kholia/HF-PA-v6/Info/5-watt-qrp-gallon-amplifier-hf-using-irf510.pdf

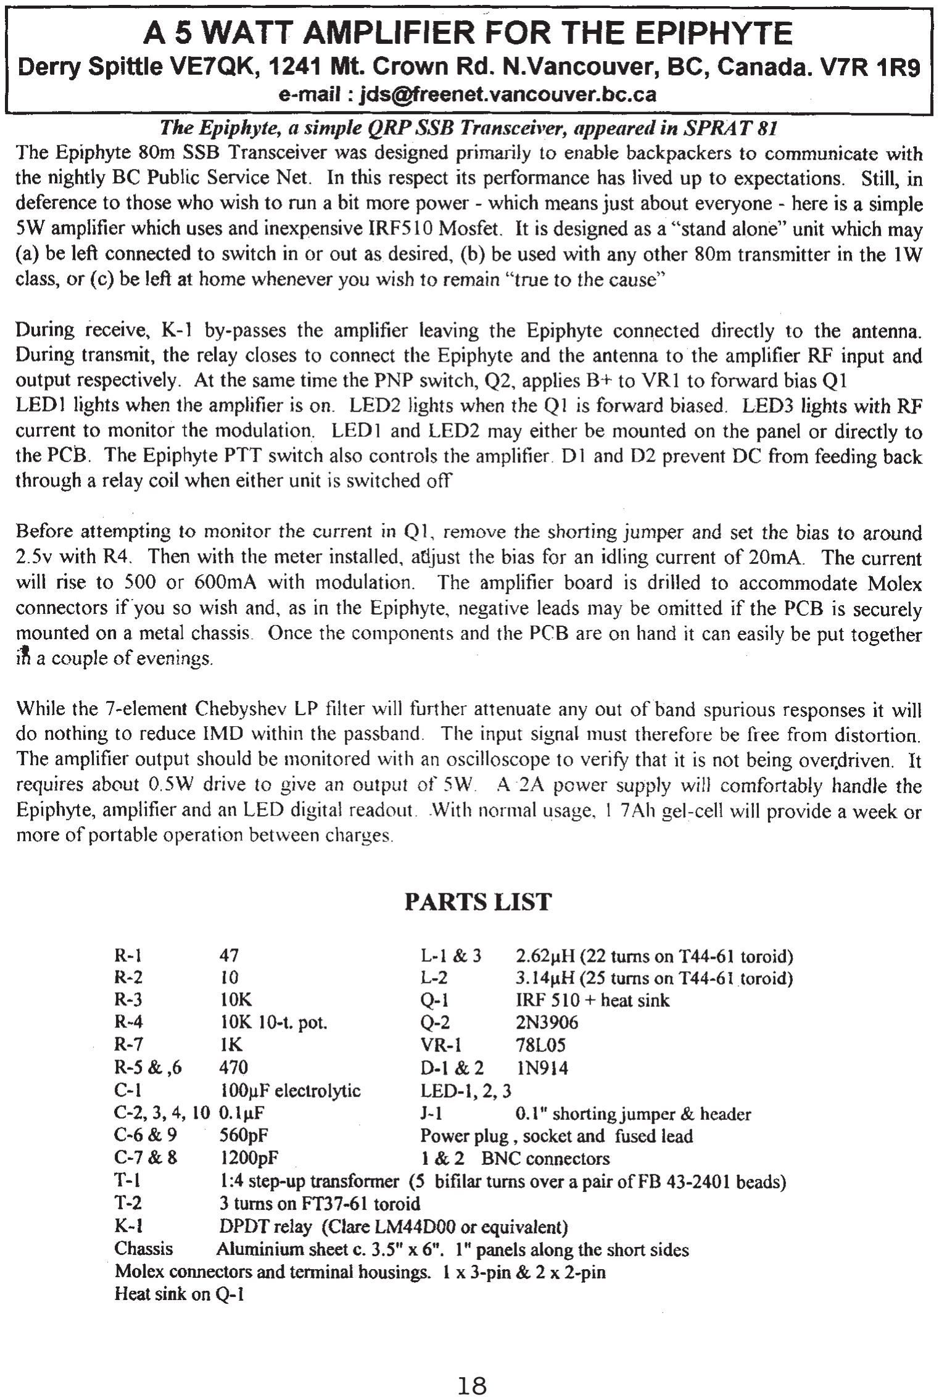
[picture p87: page 1]

18

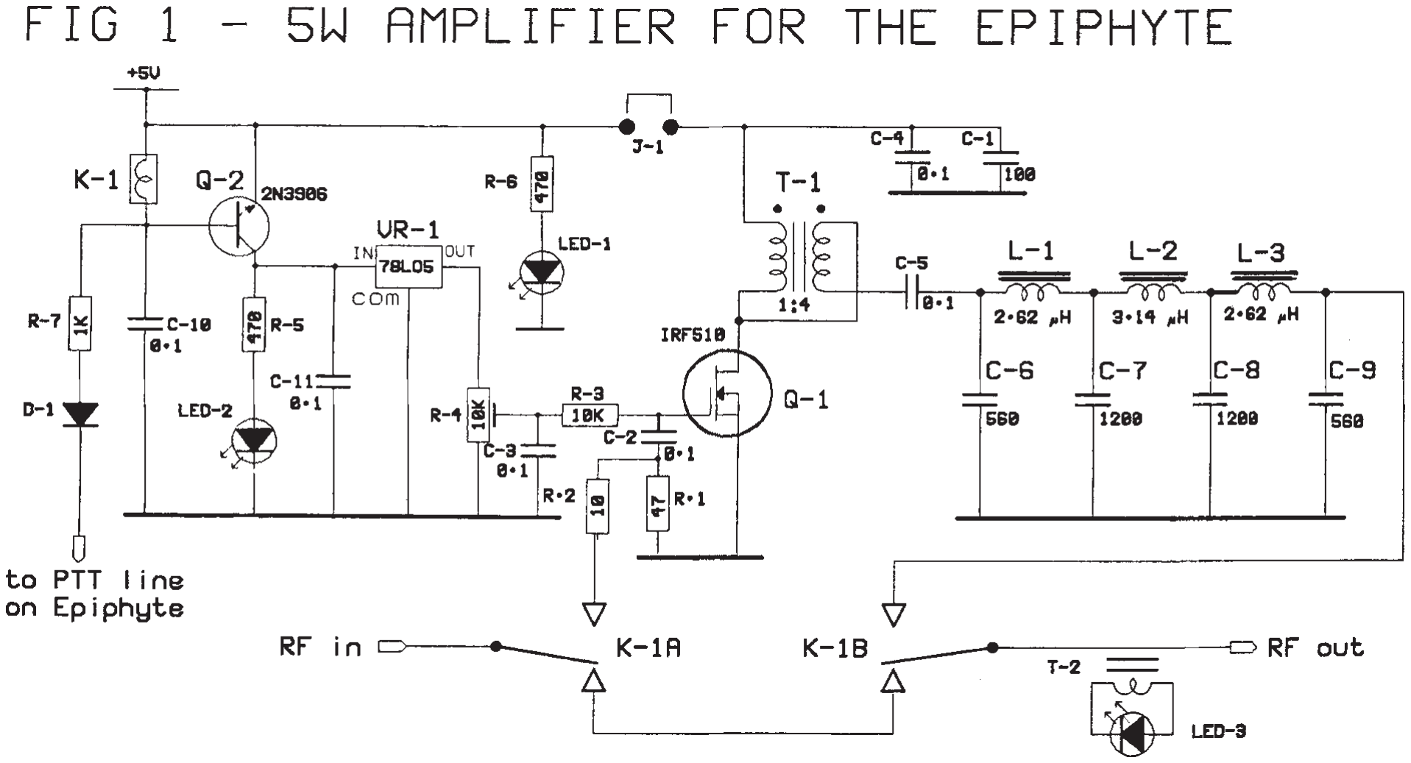
[picture p88: figure]

19

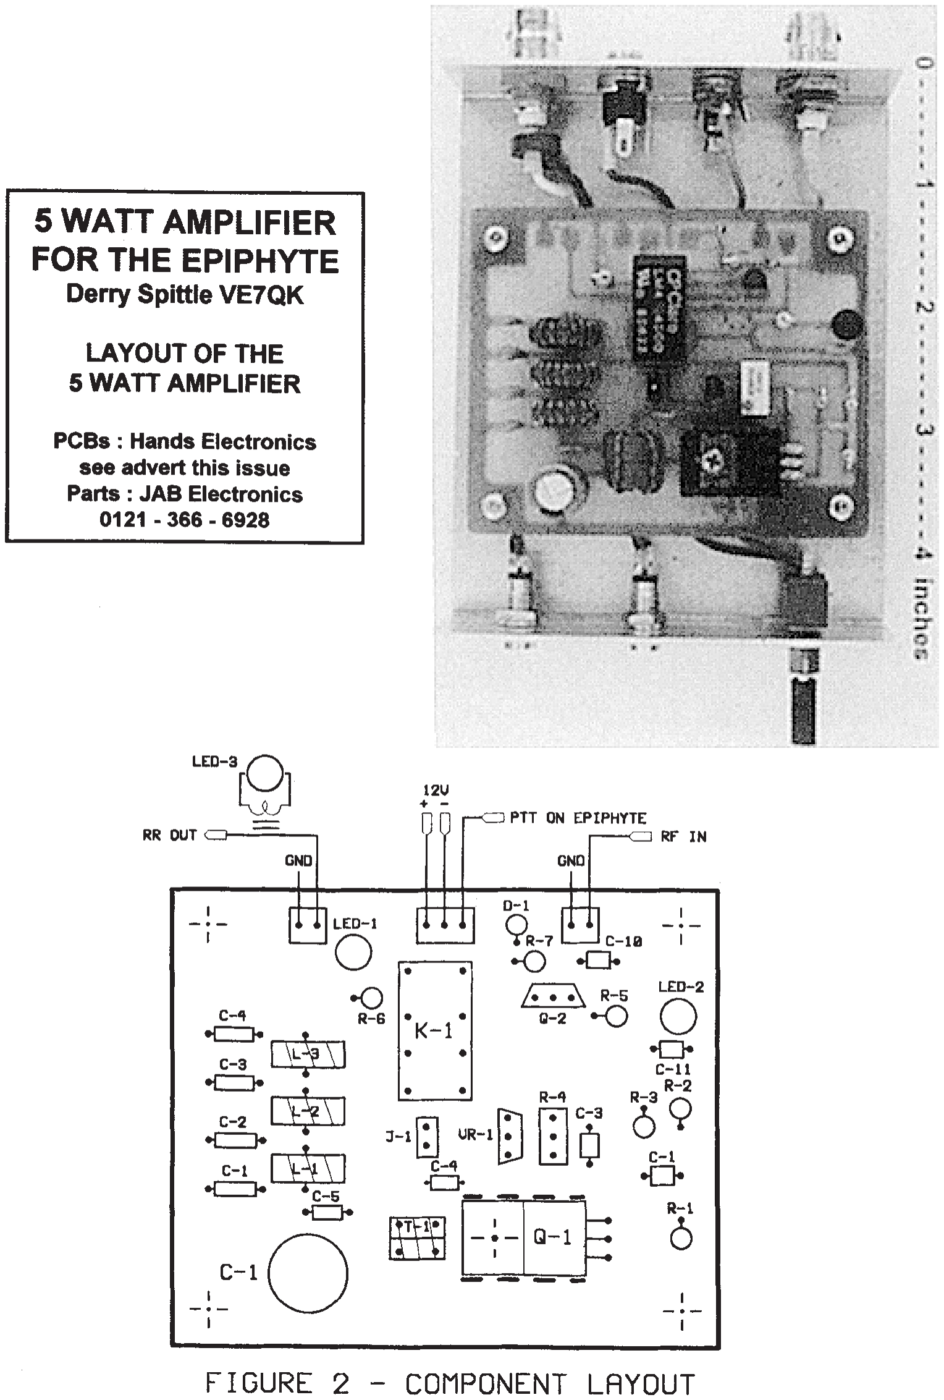
[picture p89: page 3]

20
