kholia/HF-PA-v6/datasheets/IRF9540-Pinout.jpg

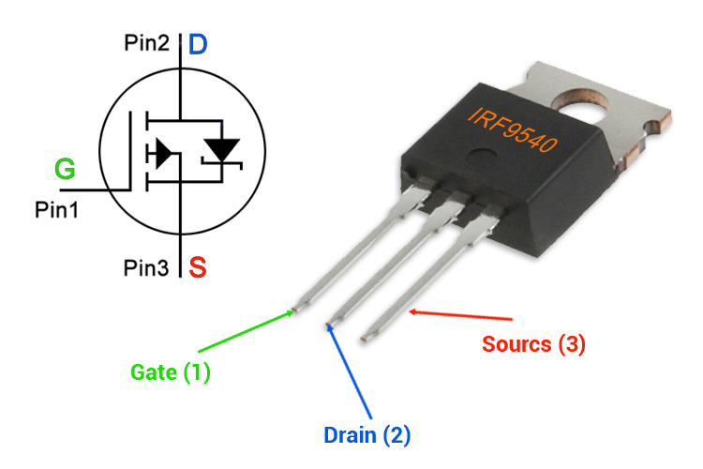
datasheets/IRF9540-Pinout.jpg
