kholia/HF-PA-v6/datasheets/Pinout of 2N2222 variants in plastic TO-92 package.jpg

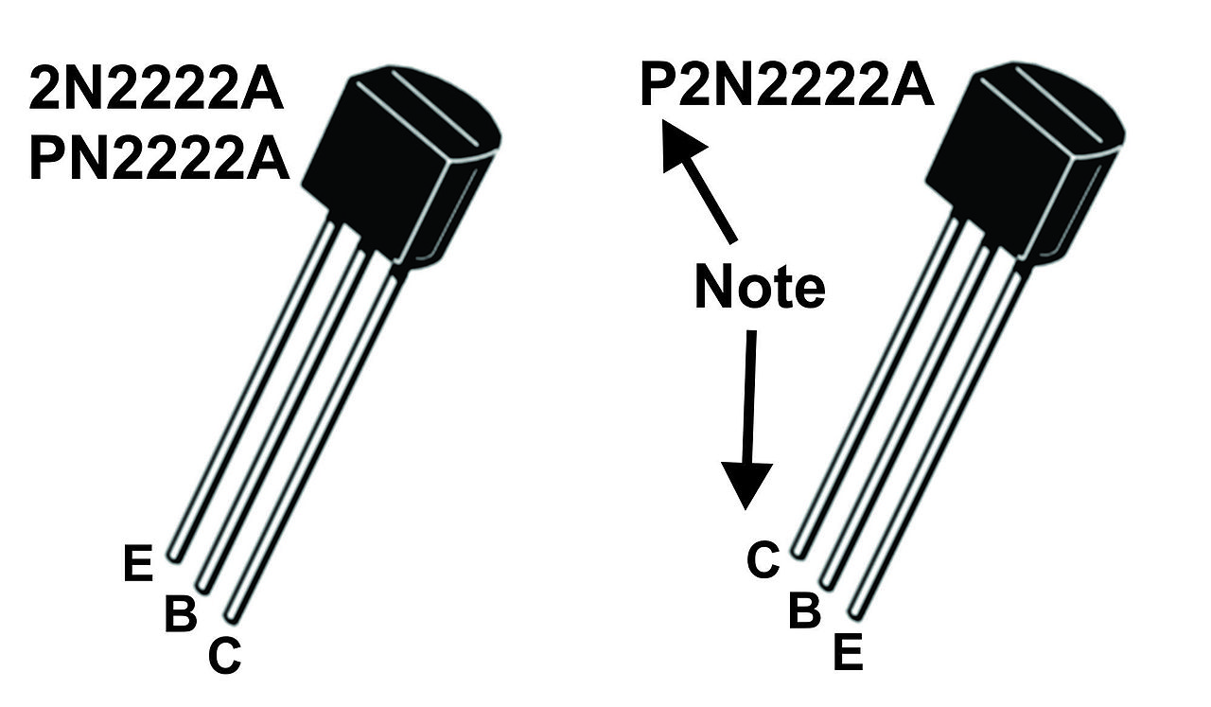
datasheets/Pinout of 2N2222 variants in plastic TO-92 package.jpg
