kholia/HF-PA-v6/datasheets/rd16hhf1-pout-vs-pin.png

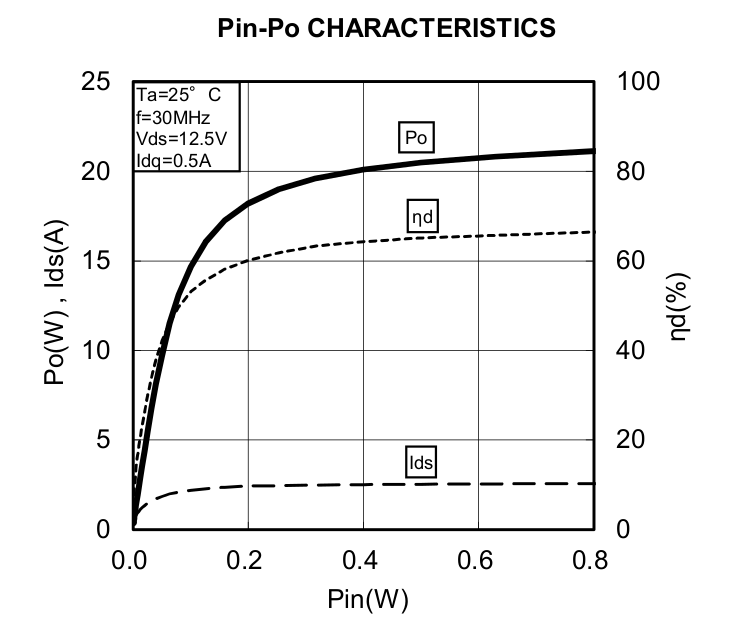
datasheets/rd16hhf1-pout-vs-pin.png
