kholia/HF-PA-v6/HF-PA-Combined/PCB-Rendering.png

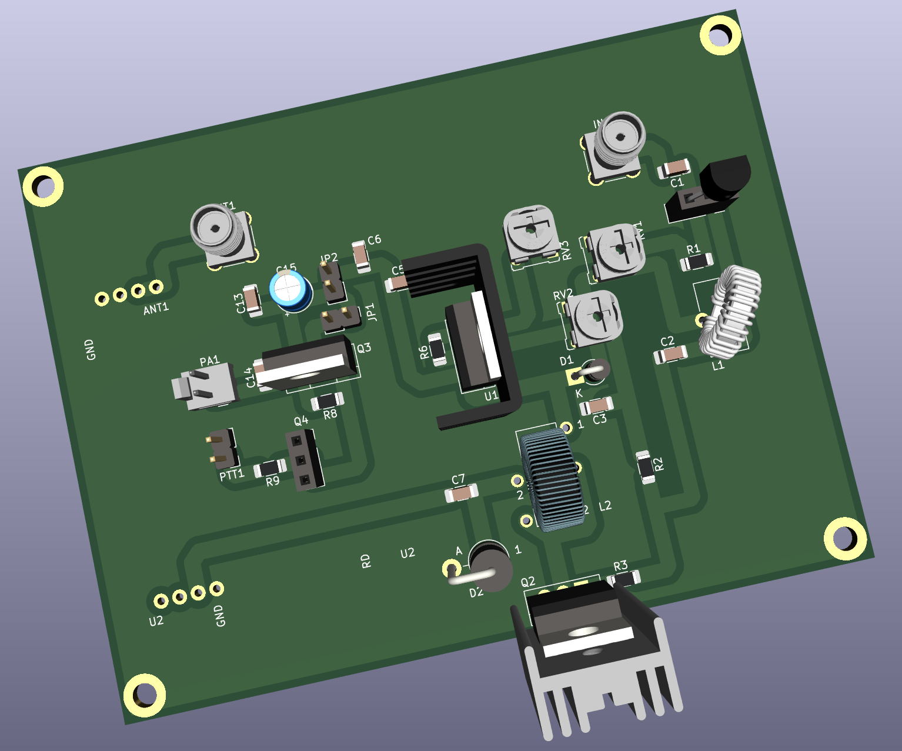
HF-PA-Combined/PCB-Rendering.png
