kholia/HF-PA-v6/Info/1W_PA_Hand_Schematic.jpg

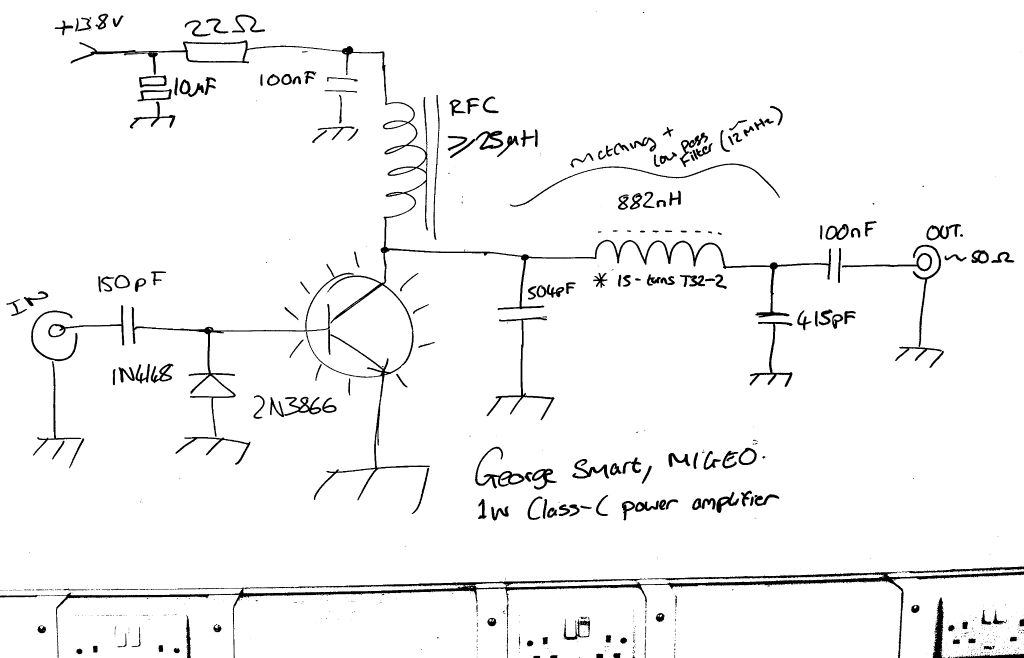
Info/1W_PA_Hand_Schematic.jpg
