kholia/HF-PA-v6/Info/1W_PA_Picture.jpg

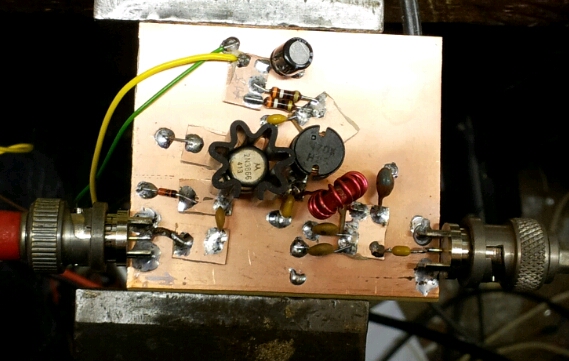
Info/1W_PA_Picture.jpg
