kholia/HF-PA-v6/Info/50MHZ_16W_MOSFET_PA.gif

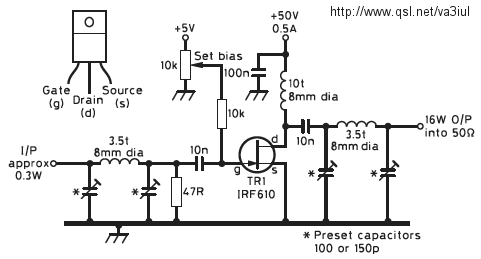
Info/50MHZ_16W_MOSFET_PA.gif
