kholia/HF-PA-v6/Info/50MHz_40W_MOSFET_PA_DJ9FG.gif

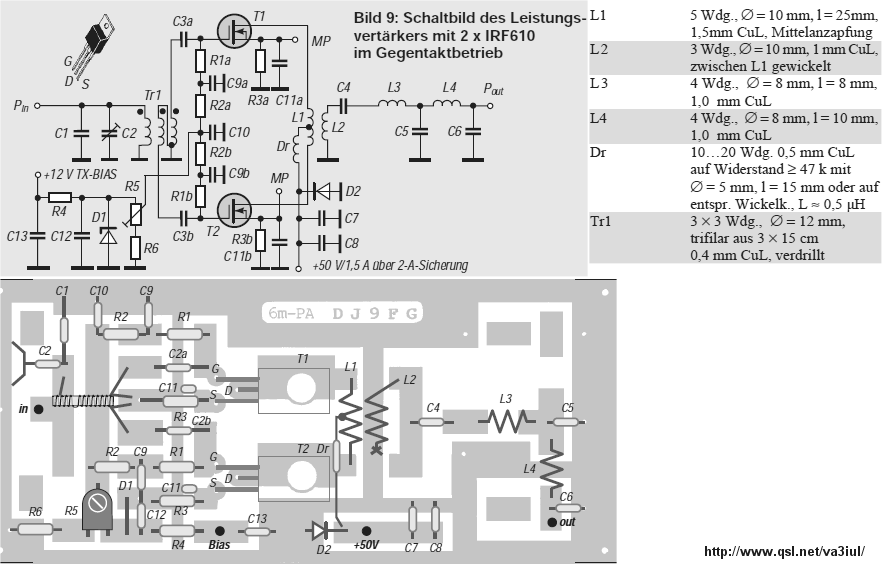
Info/50MHz_40W_MOSFET_PA_DJ9FG.gif
