kholia/HF-PA-v6/Info/"Idq".png

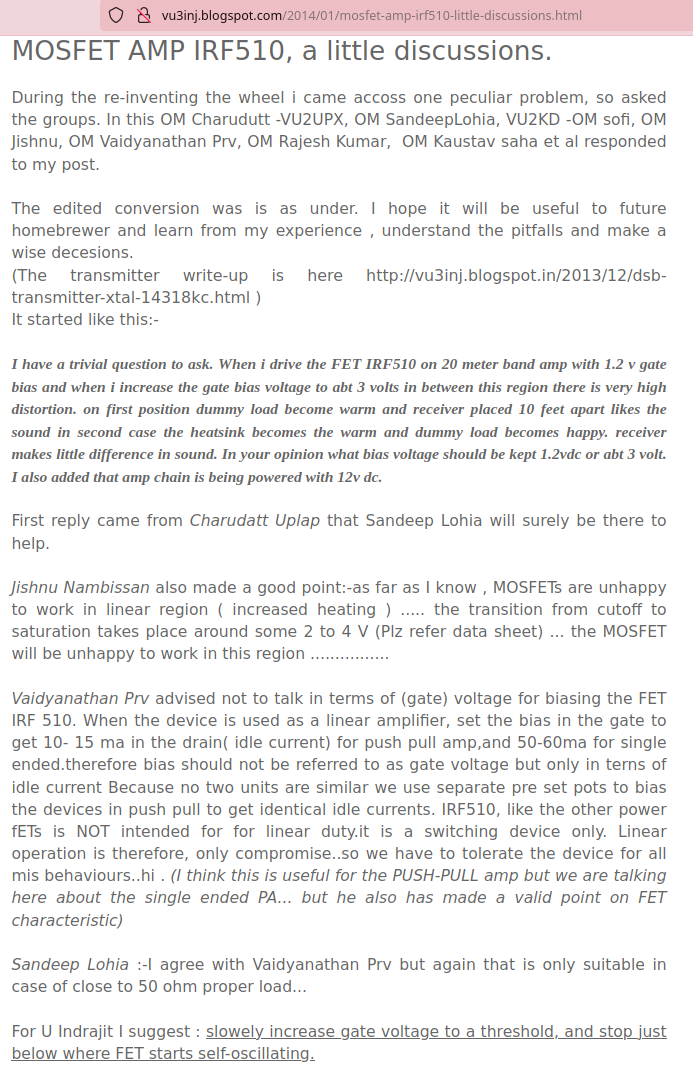
Info/"Idq".png
