kholia/HF-PA-v6/Info/(220)_ZX-SSB_II_PA.png

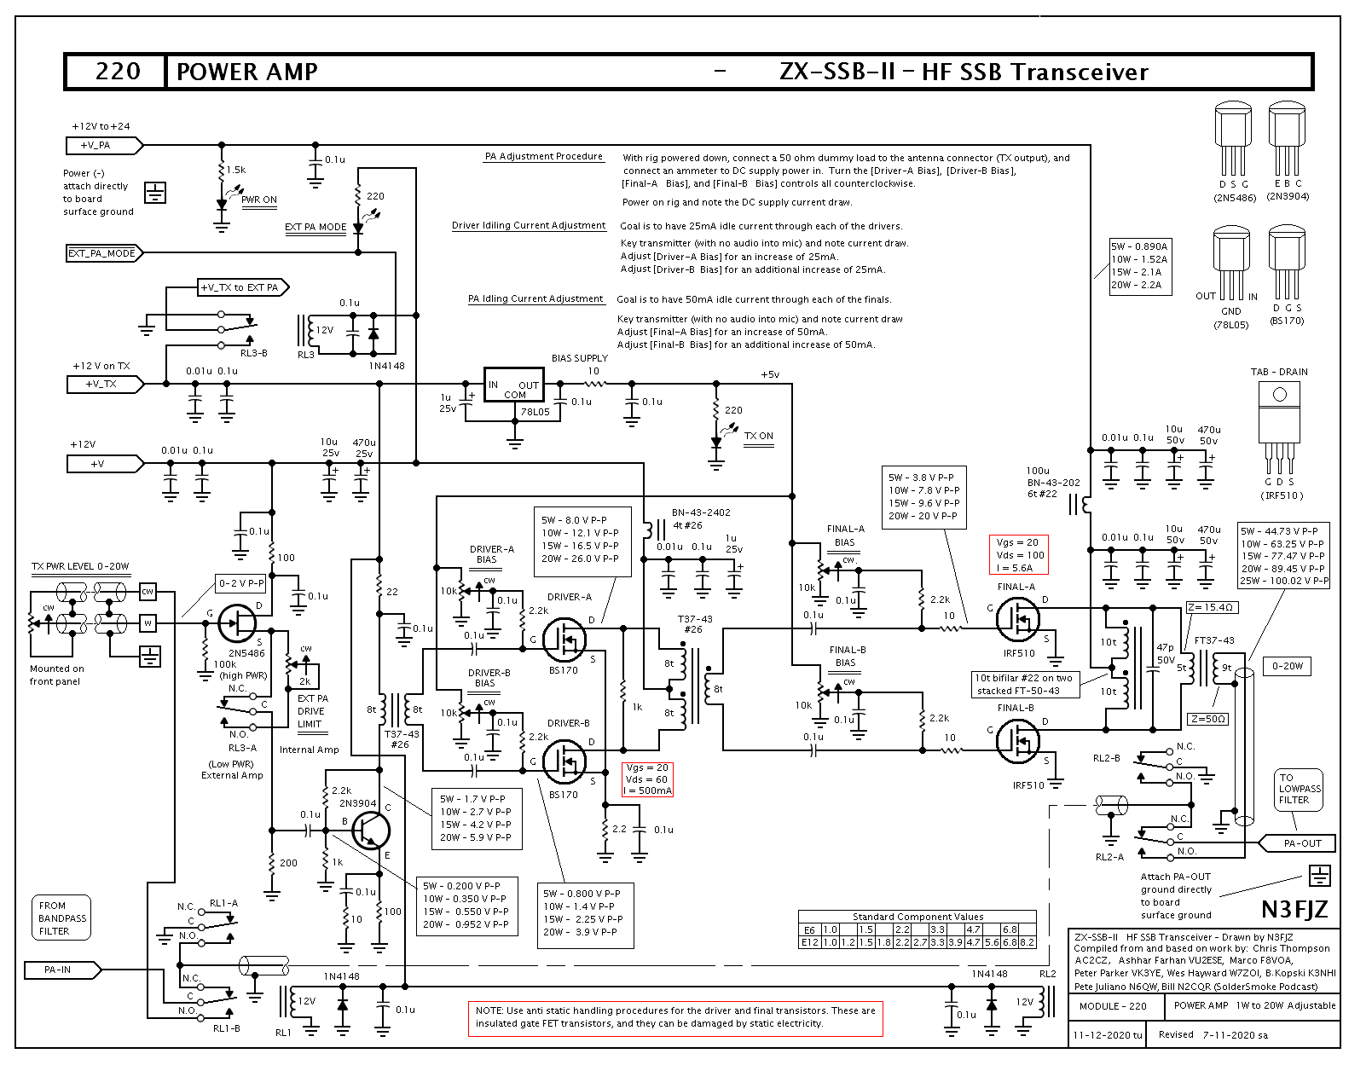
Info/(220)_ZX-SSB_II_PA.png
