kholia/HF-PA-v6/Info/(230-ALL)_ZX-SSB-II_Lowpass_filter_all_bands.png

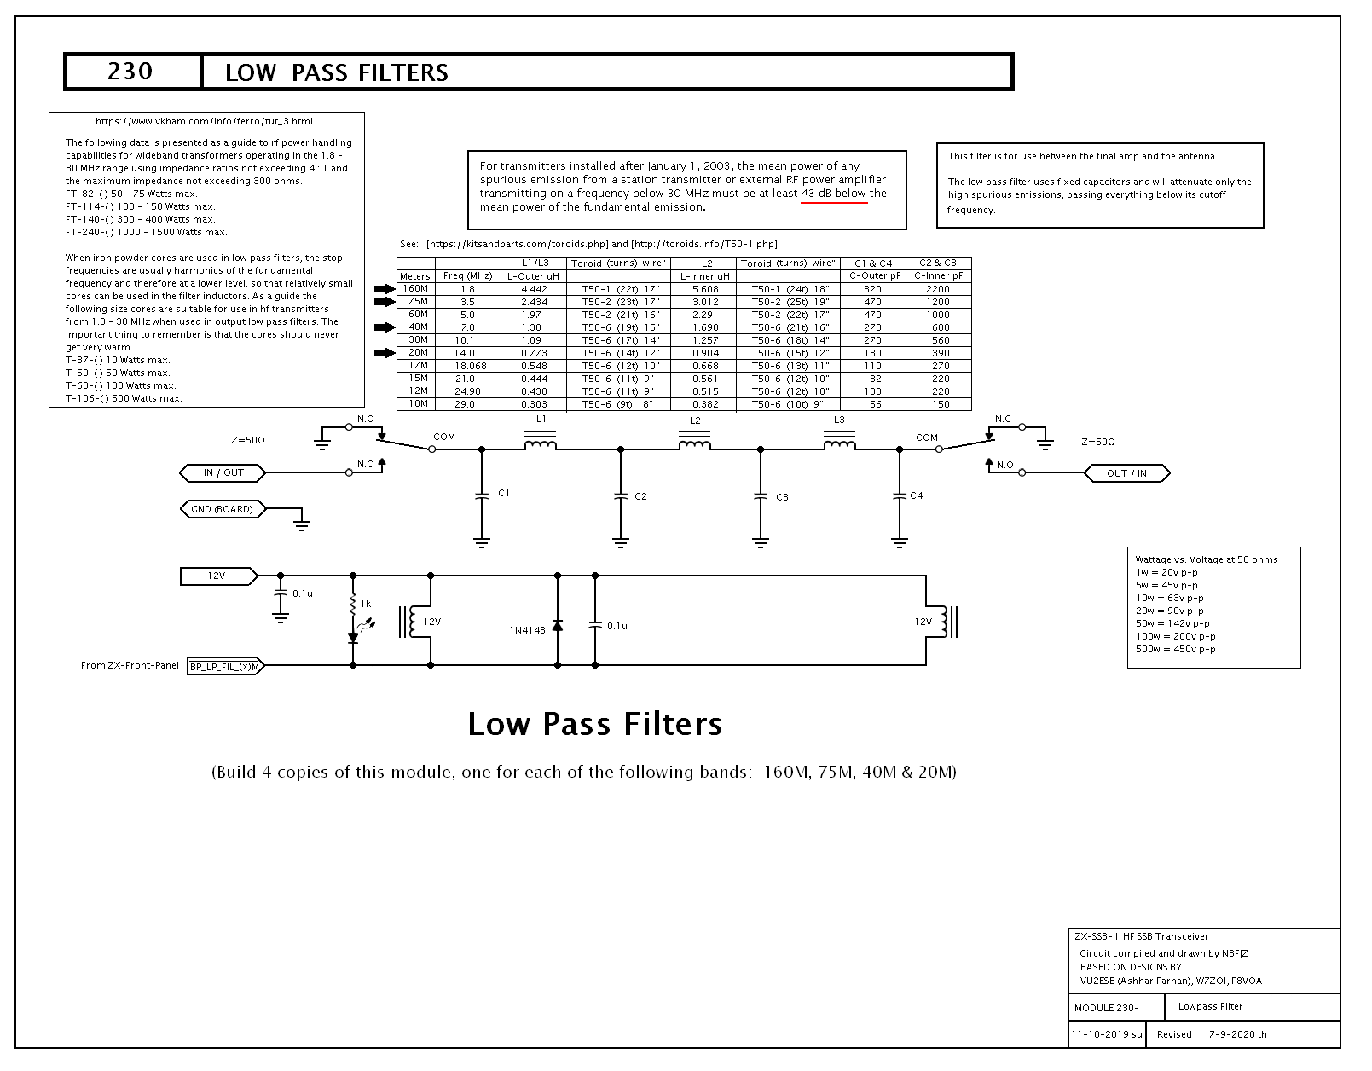
Info/(230-ALL)_ZX-SSB-II_Lowpass_filter_all_bands.png
