kholia/HF-PA-v6/Info/Ampacity-Screenshot_2021-09-23_20-11-56.png

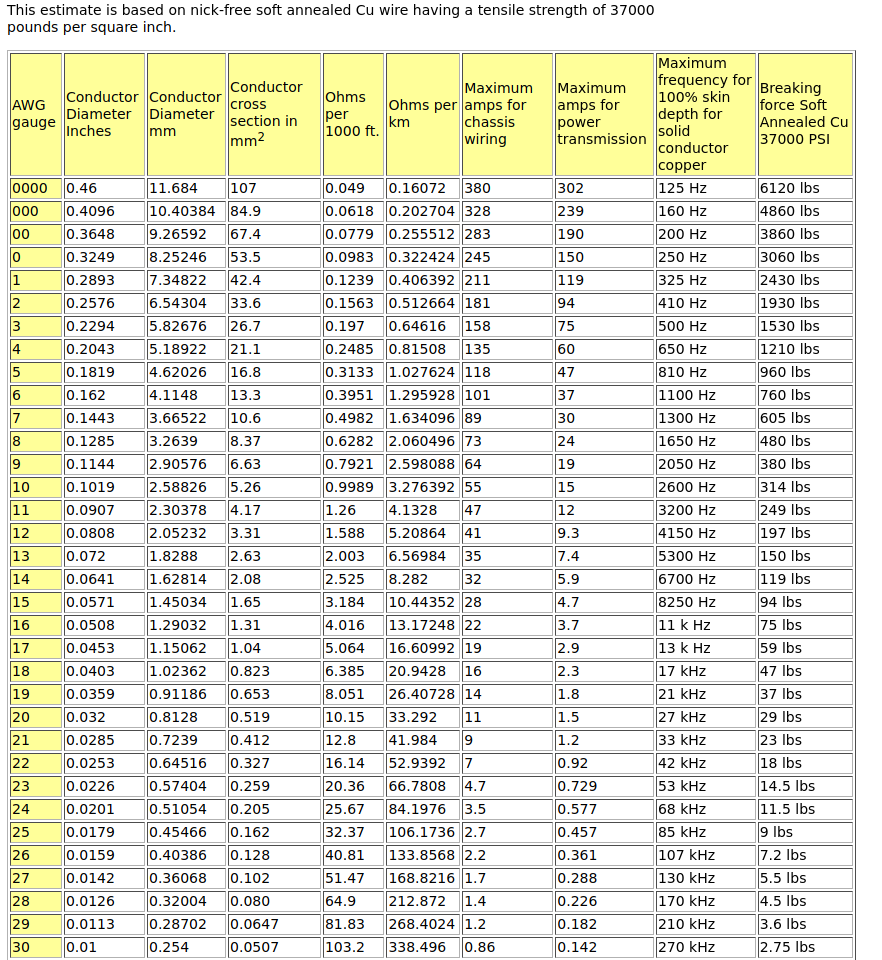
Info/Ampacity-Screenshot_2021-09-23_20-11-56.png
