kholia/HF-PA-v6/Info/BD139 Note.png

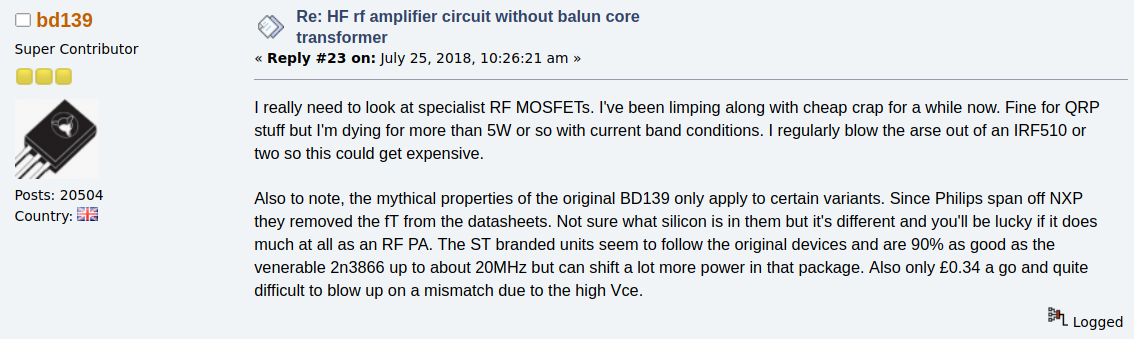
Info/BD139 Note.png
