kholia/HF-PA-v6/Info/Fake 7805 CV - Mar 2018.jpeg

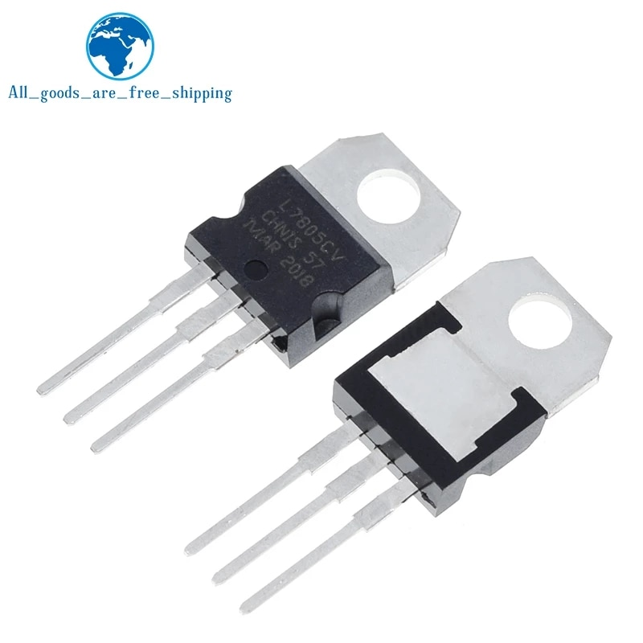
Info/Fake 7805 CV - Mar 2018.jpeg
