kholia/HF-PA-v6/Info/Fake ST 7805 - 1718.jpg

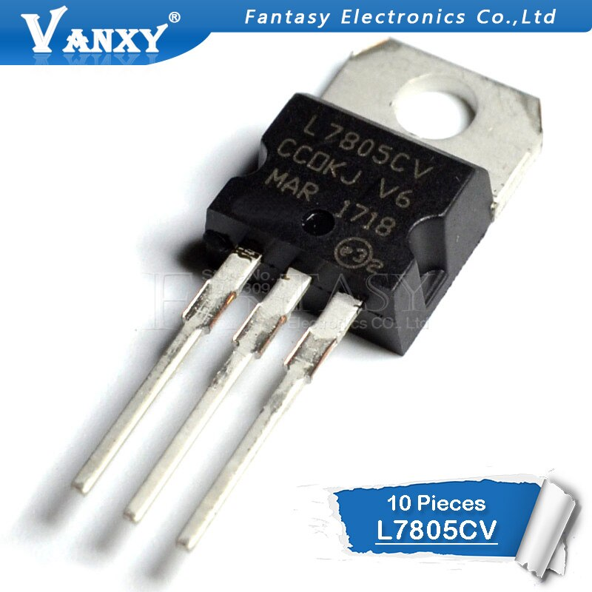
Info/Fake ST 7805 - 1718.jpg
