kholia/HF-PA-v6/Info/Fake ST 7805.jpg

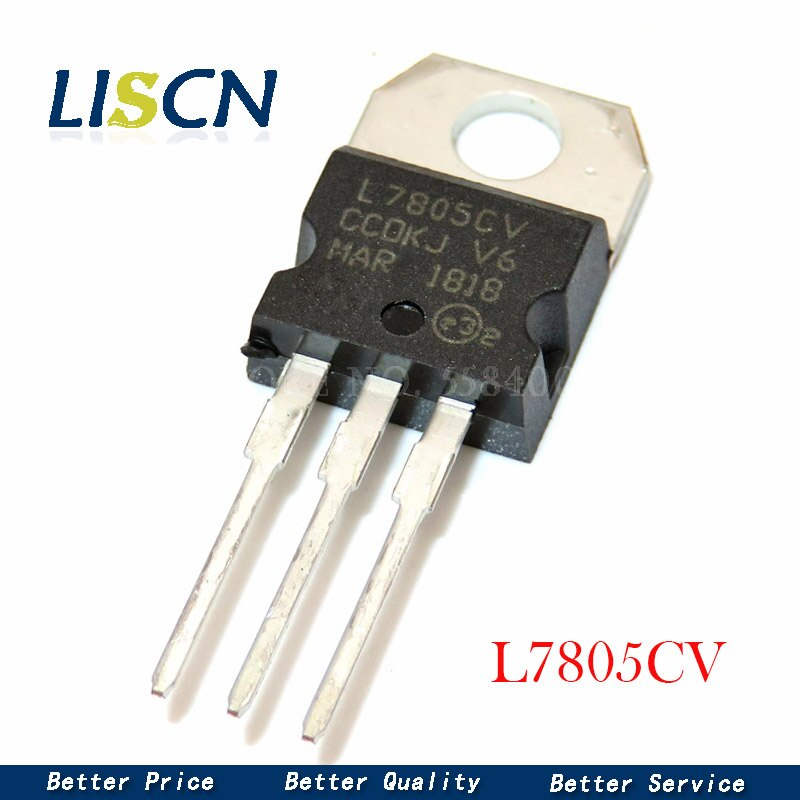
Info/Fake ST 7805.jpg
