kholia/HF-PA-v6/Info/Fake ST 7805.webp

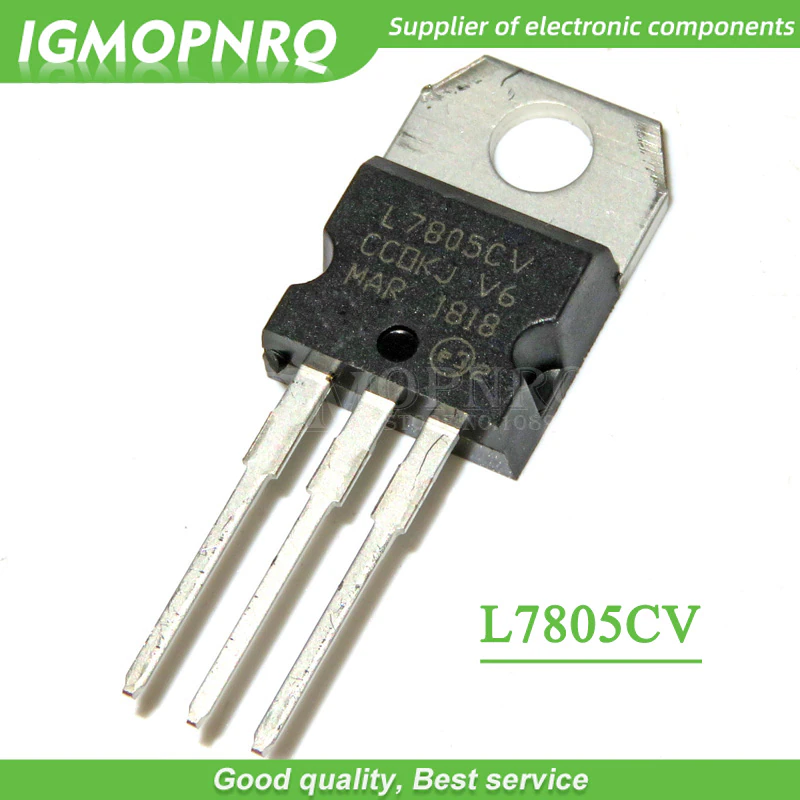
Info/Fake ST 7805.webp
