kholia/HF-PA-v6/Info/IRF530-SEC-TO-220.jpg

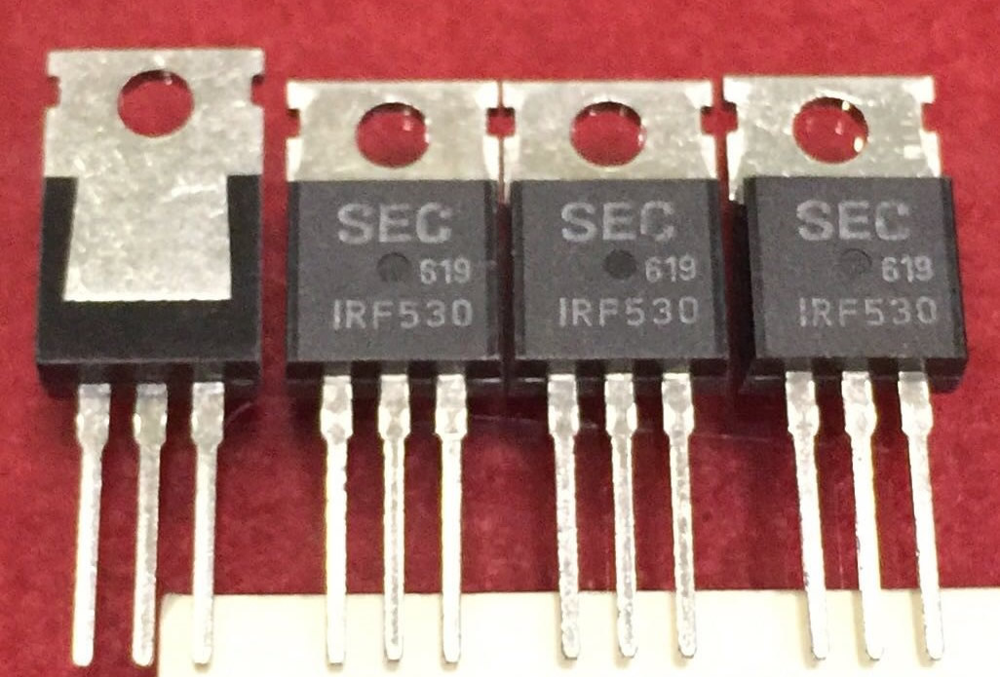
Info/IRF530-SEC-TO-220.jpg
