kholia/HF-PA-v6/Info/IRF610.jpg

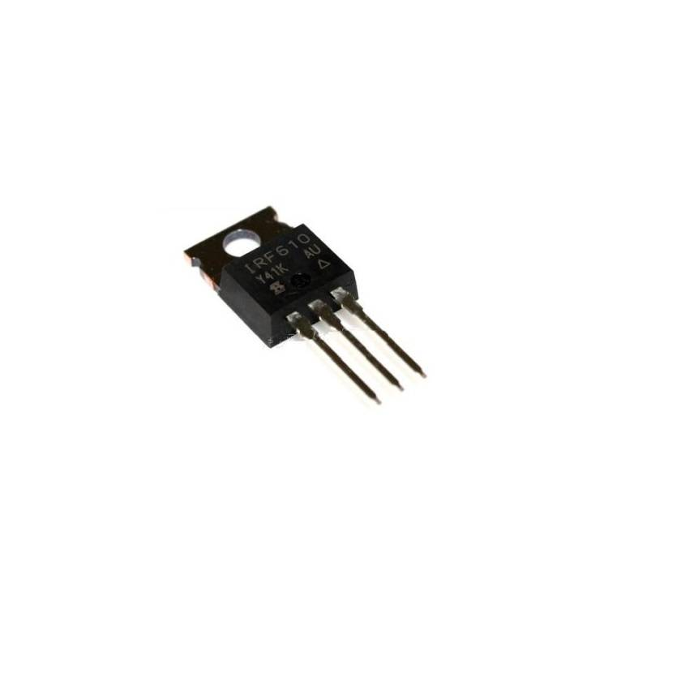
Info/IRF610.jpg
