kholia/HF-PA-v6/Info/LM7805 Pinout.jpg

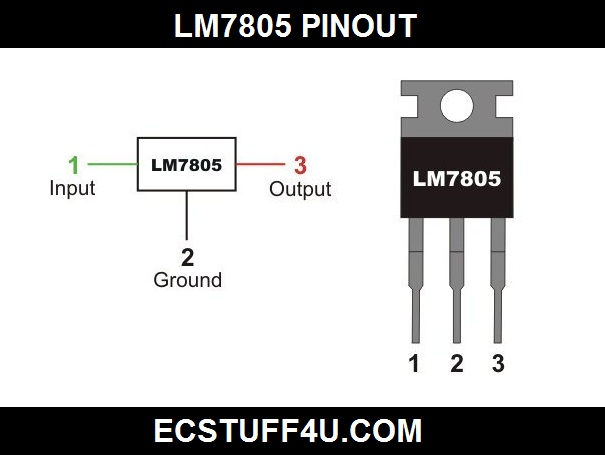
Info/LM7805 Pinout.jpg
