kholia/HF-PA-v6/Info/NTE224.jpg

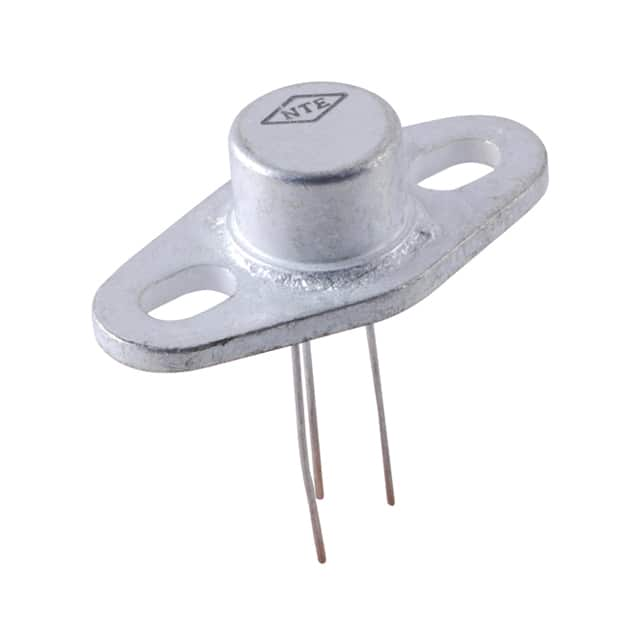
Info/NTE224.jpg
