kholia/HF-PA-v6/Info/pa-1200x900.jpg

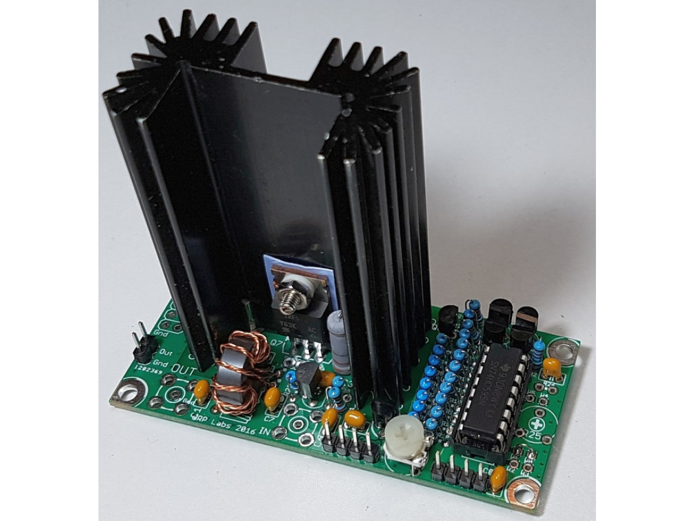
Info/pa-1200x900.jpg
