kholia/HF-PA-v6/Info/peanuts.GIF

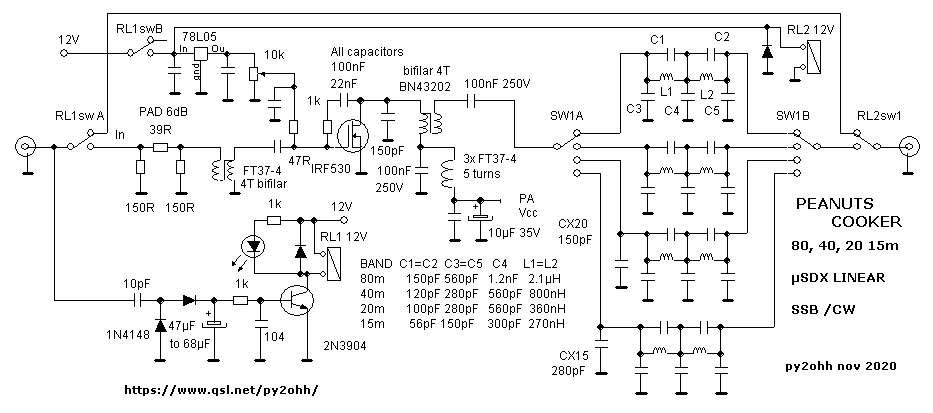
Info/peanuts.GIF
