kholia/HF-PA-v6/Info/PowerFreq1.gif

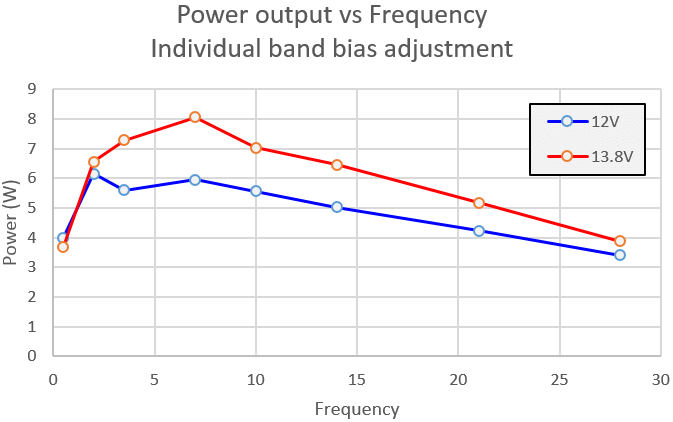
Info/PowerFreq1.gif
