kholia/HF-PA-v6/Info/PowerSupply1.gif

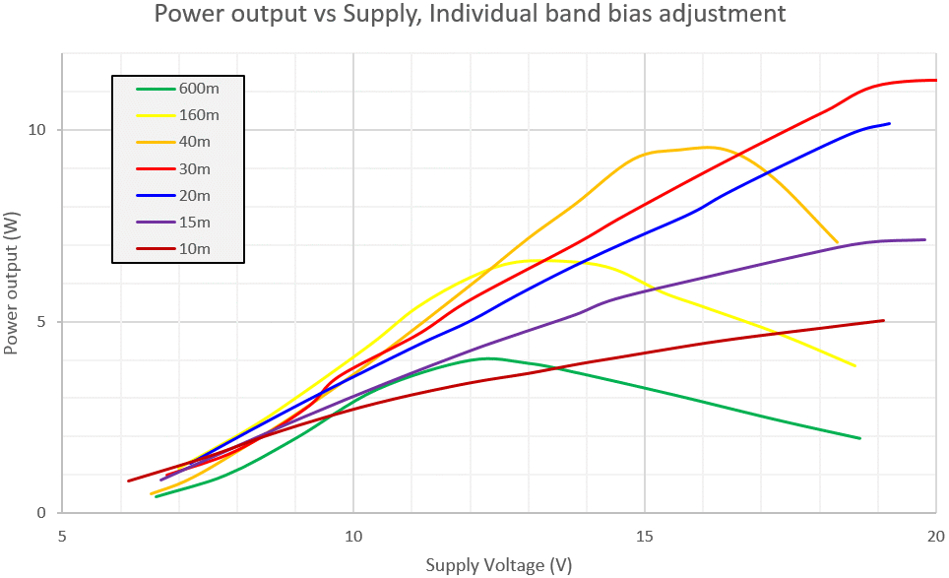
Info/PowerSupply1.gif
