kholia/HF-PA-v6/Info/QRP Labs HF PA 5W.png

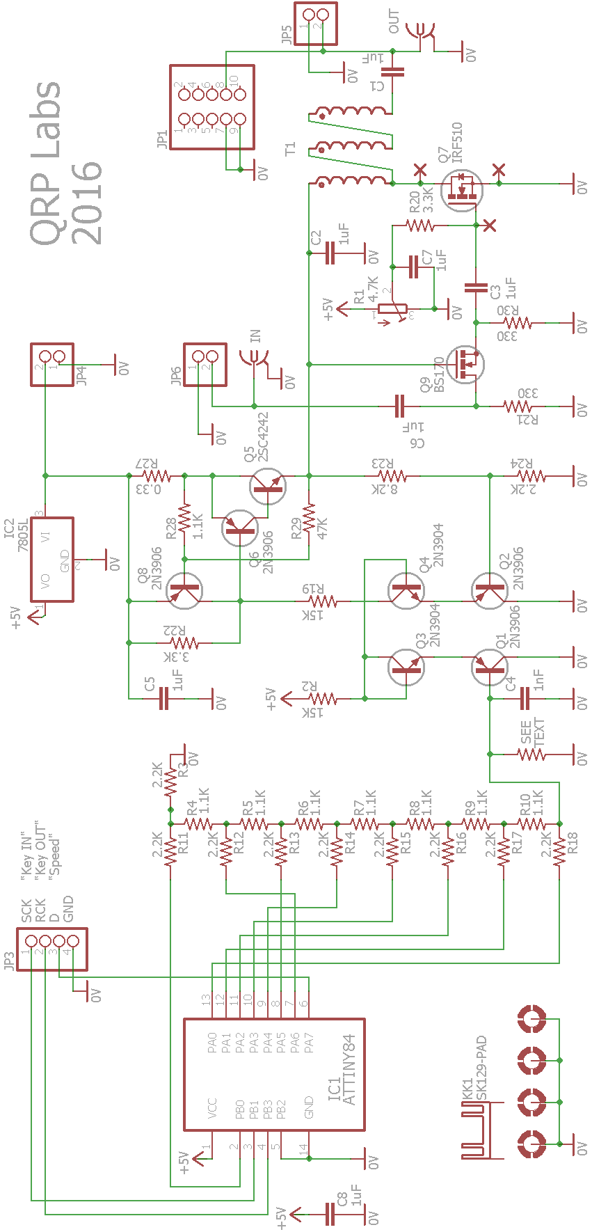
Info/QRP Labs HF PA 5W.png
