kholia/HF-PA-v6/Info/QRP-LABS-TX-switch.png

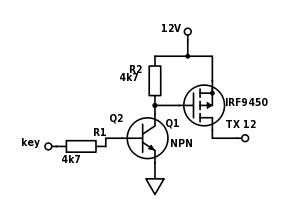
Info/QRP-LABS-TX-switch.png
