kholia/HF-PA-v6/Info/Recommended-PSU-2021-10-14-17.16.32.jpg

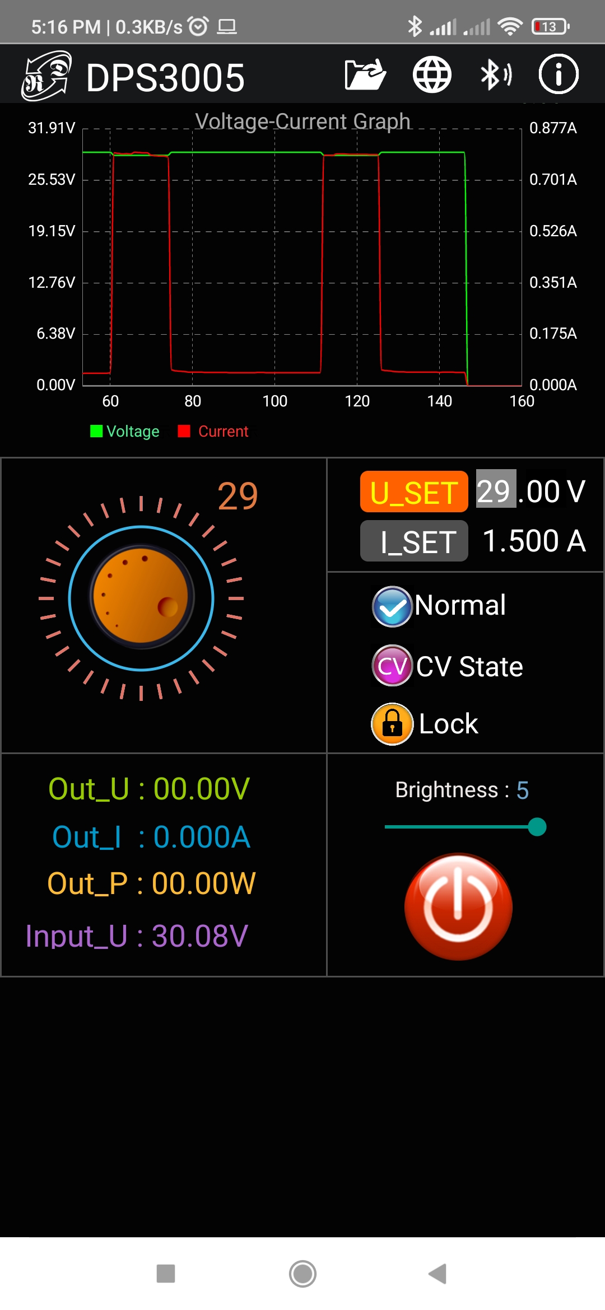
Info/Recommended-PSU-2021-10-14-17.16.32.jpg
