kholia/HF-PA-v6/Info/schematic.jpg

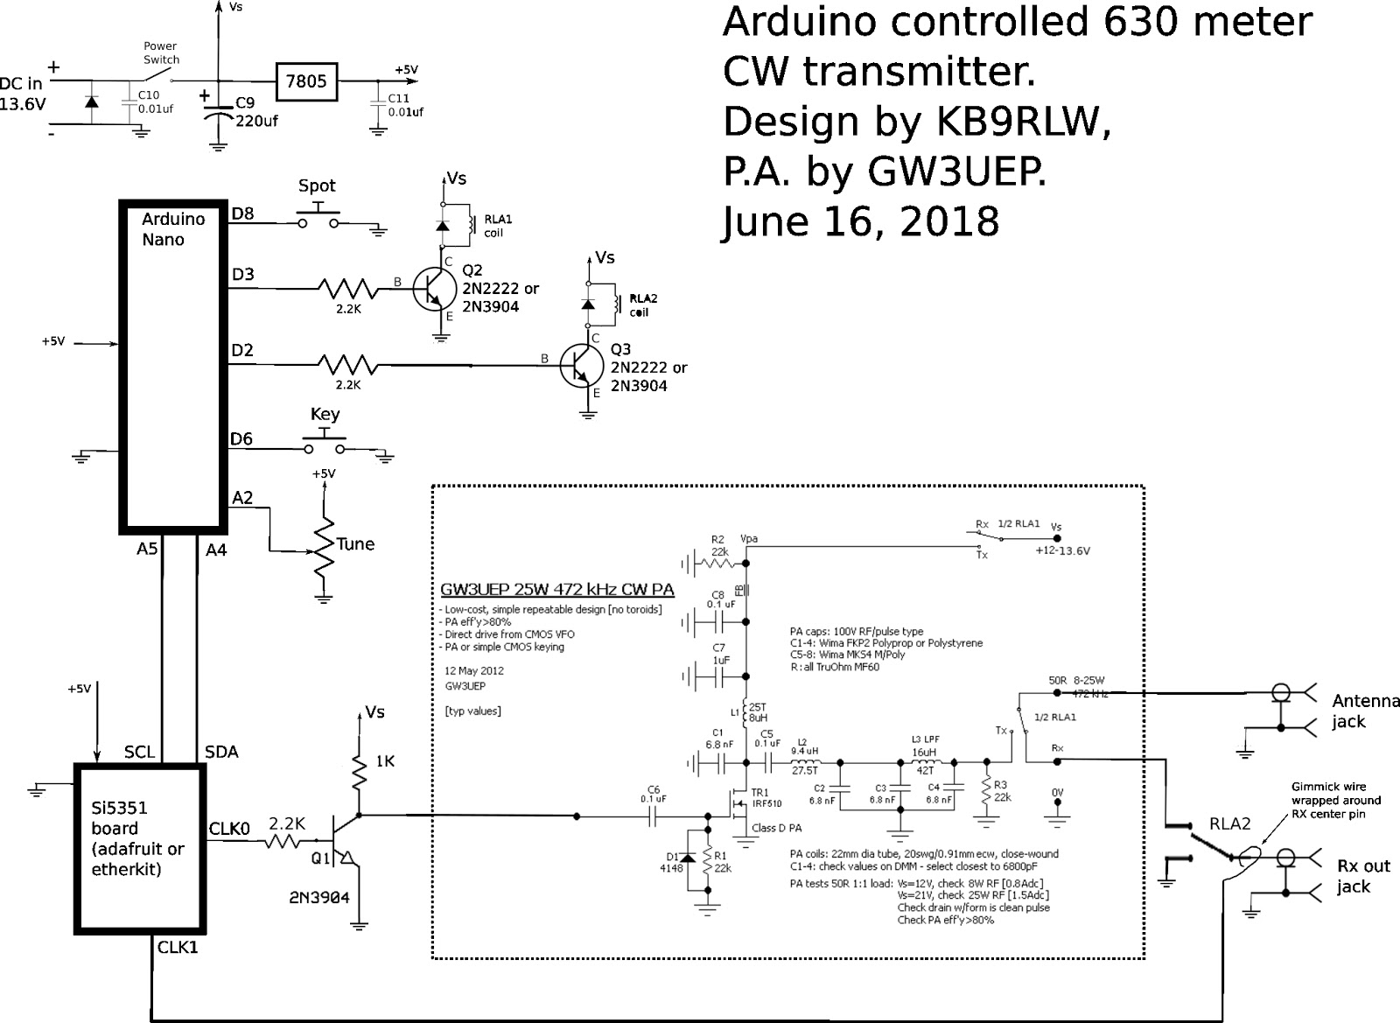
Info/schematic.jpg
