kholia/HF-PA-v6/Info/Screenshot_2021-09-22_15-32-31.png

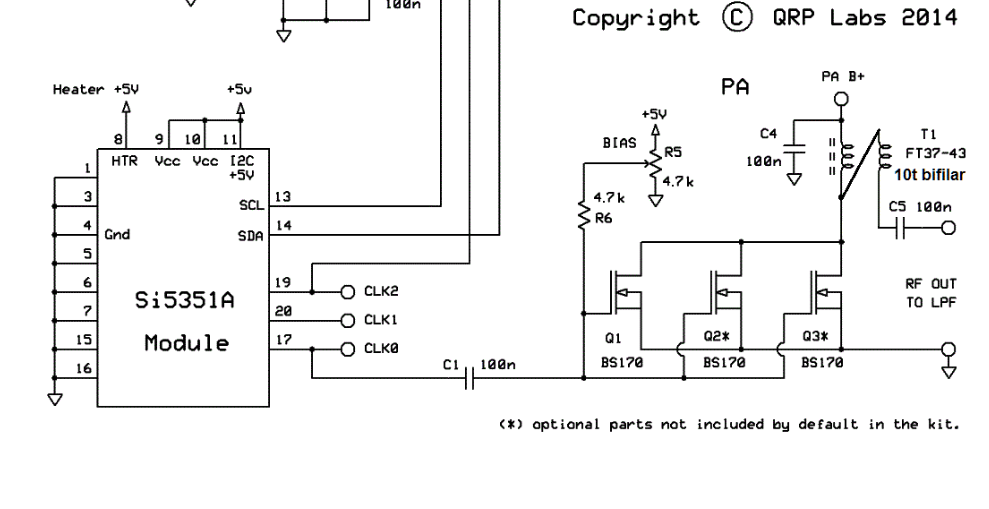
Info/Screenshot_2021-09-22_15-32-31.png
