kholia/HF-PA-v6/Info/Screenshot_2021-09-23_20-14-42.png

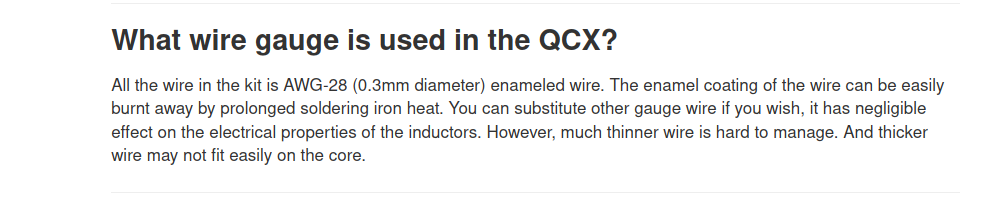
Info/Screenshot_2021-09-23_20-14-42.png
