kholia/HF-PA-v6/Info/Screenshot_2021-10-03_17-21-05.png

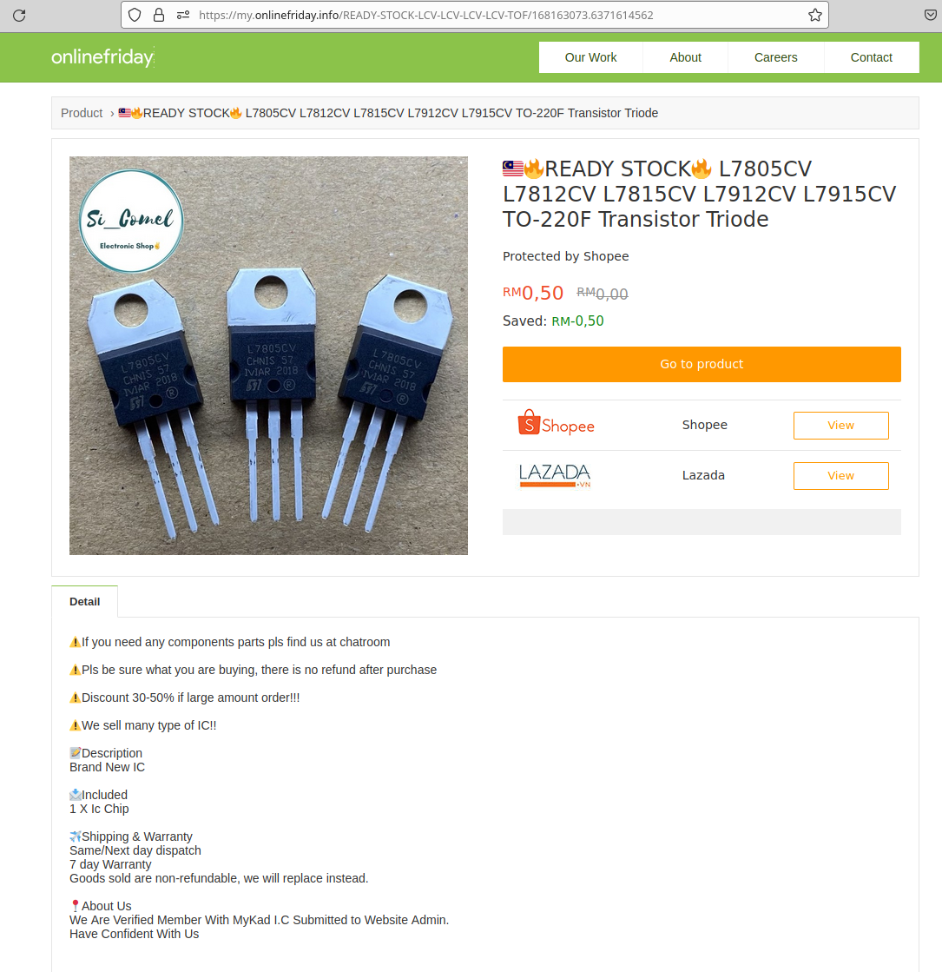
Info/Screenshot_2021-10-03_17-21-05.png
