kholia/HF-PA-v6/Info/Screenshot_2022-04-05_15-10-16.png

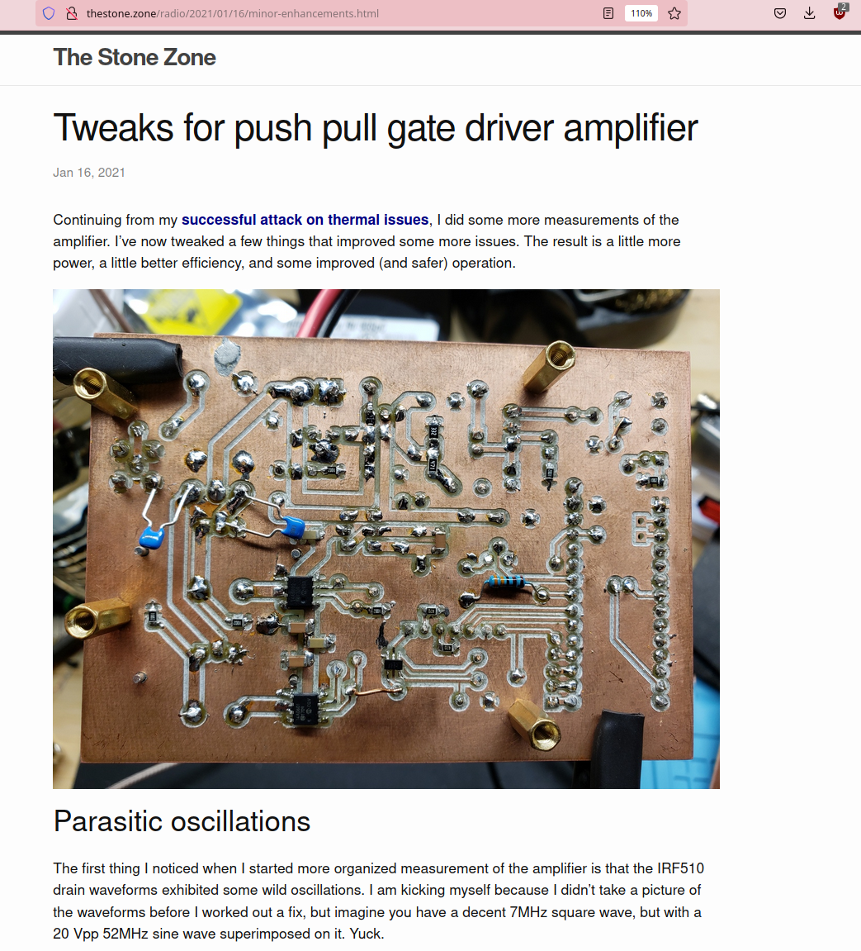
Info/Screenshot_2022-04-05_15-10-16.png
