kholia/HF-PA-v6/Info/Screenshot_2022-04-24_12-41-55.png

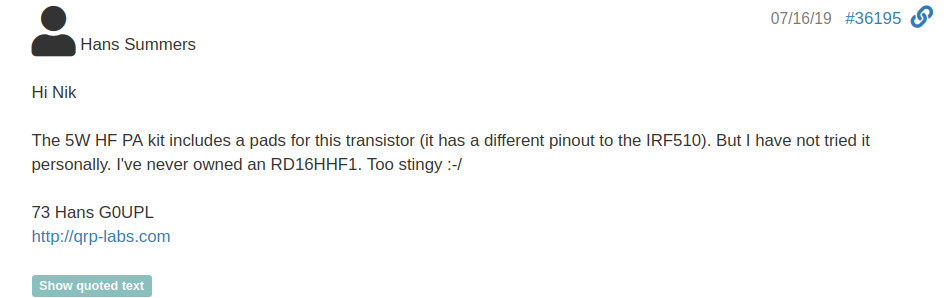
Info/Screenshot_2022-04-24_12-41-55.png
