kholia/HF-PA-v6/Info/tx80m-000.png

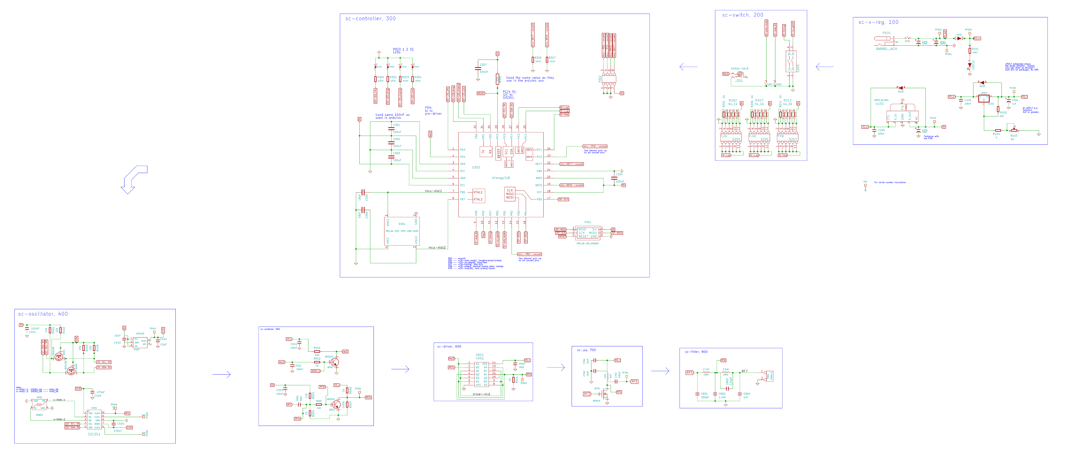
Info/tx80m-000.png
