kholia/HF-PA-v6/Info/VU2ESE-Linear-20131122_081706.jpg

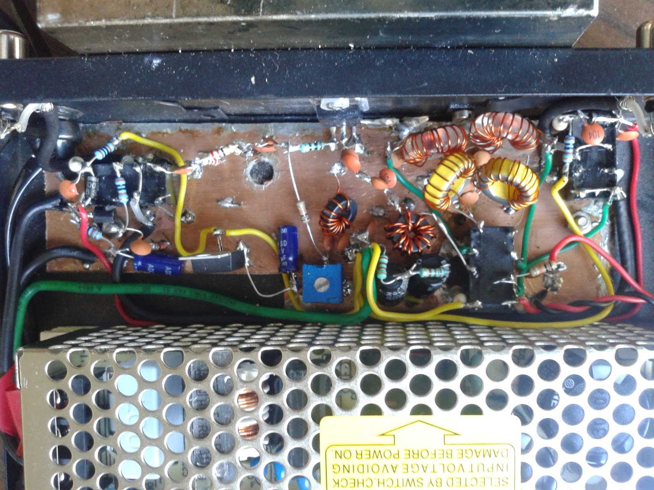
Info/VU2ESE-Linear-20131122_081706.jpg
