kholia/HF-PA-v6/LPF-Rendering-1.png

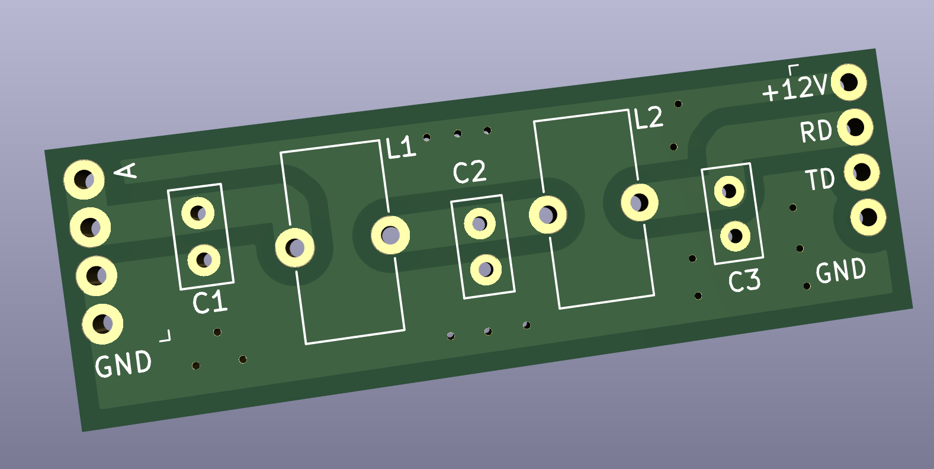
LPF-Rendering-1.png
