kholia/HF-PA-v6/Matching+LPF/Screenshot_2022-03-06_22-29-20.png

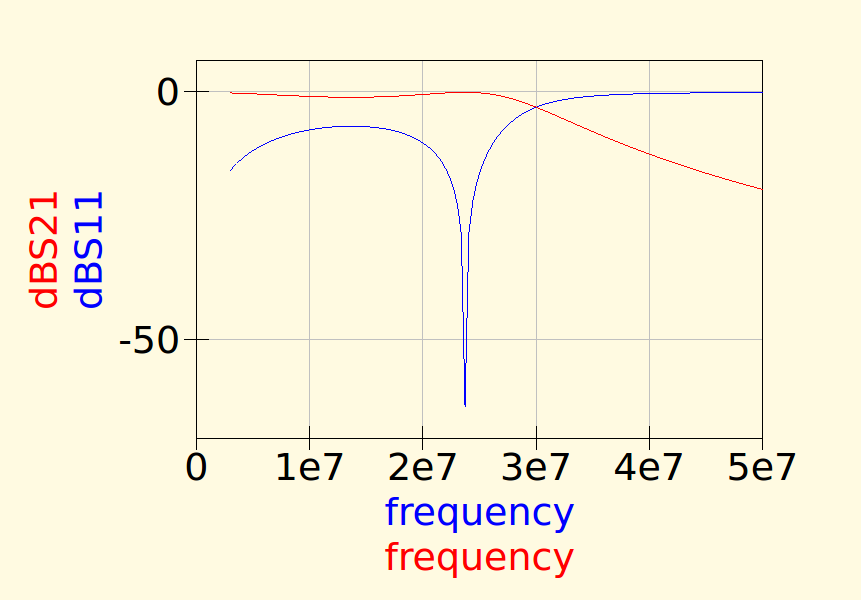
Matching+LPF/Screenshot_2022-03-06_22-29-20.png
