kholia/HF-PA-v6/Power-Block.png

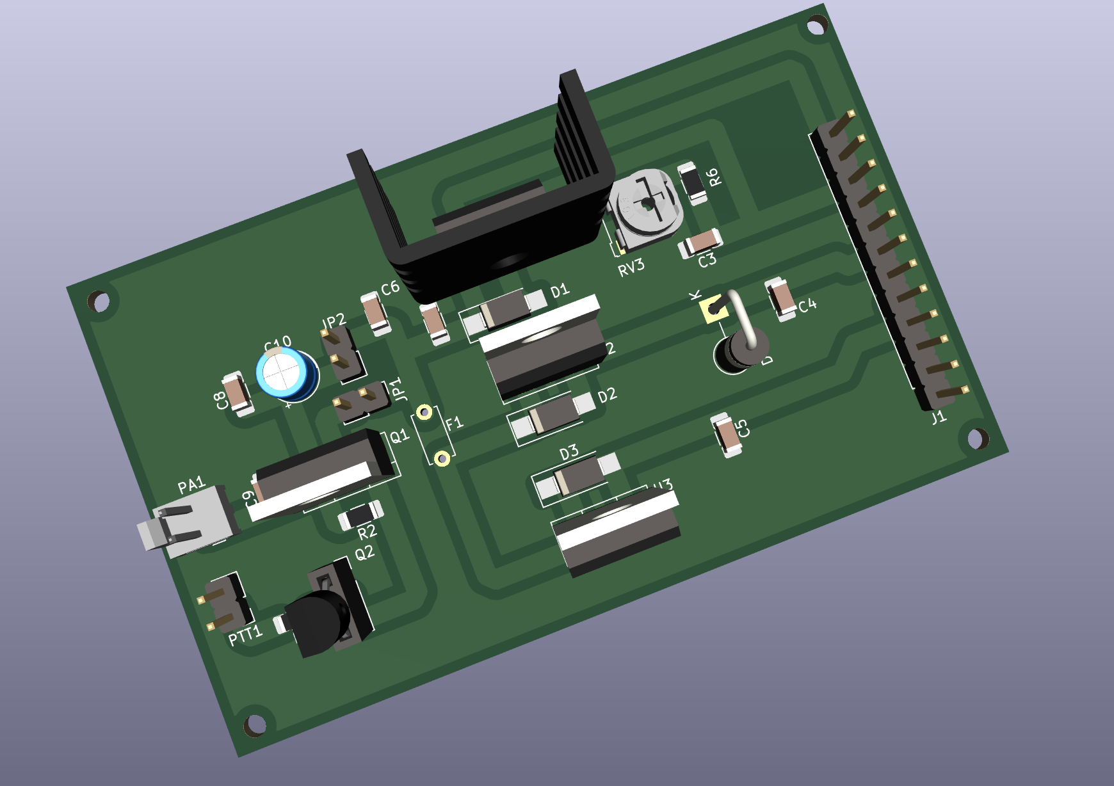
Power-Block.png
