kholia/HF-PA-v6/screenshots/6W-Fiji-Screenshot_2022-04-08_16-28-01.png

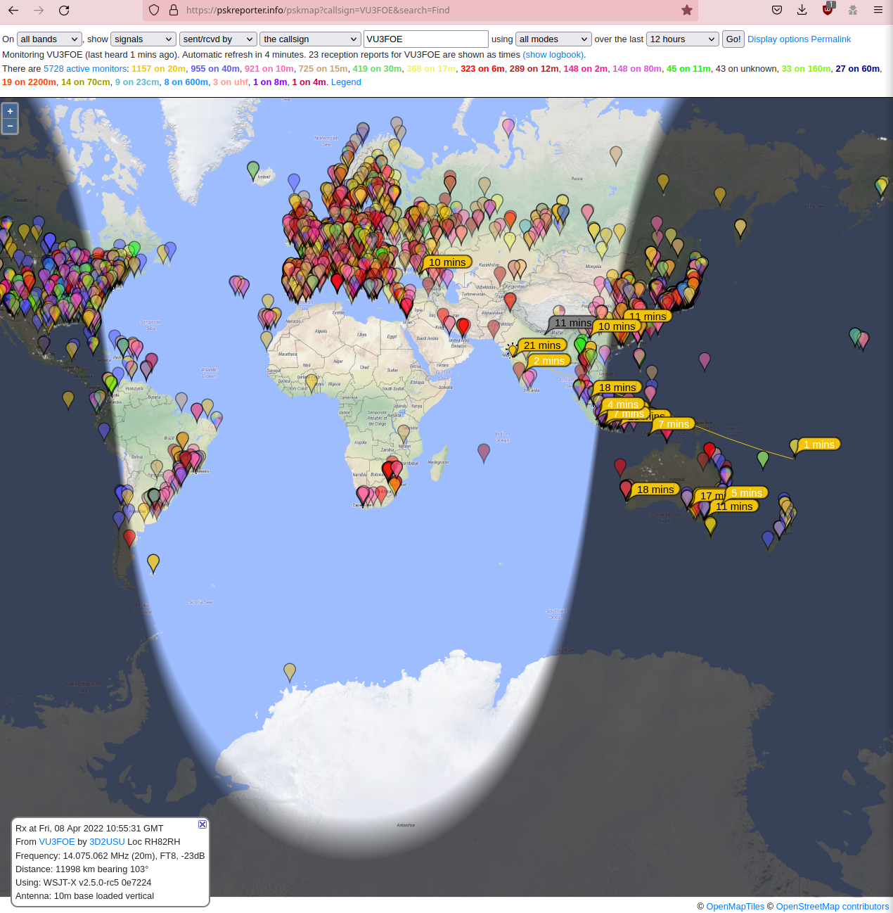
screenshots/6W-Fiji-Screenshot_2022-04-08_16-28-01.png
