kholia/HF-PA-v6/screenshots/6W-Screenshot_2022-04-08_20-03-49.png

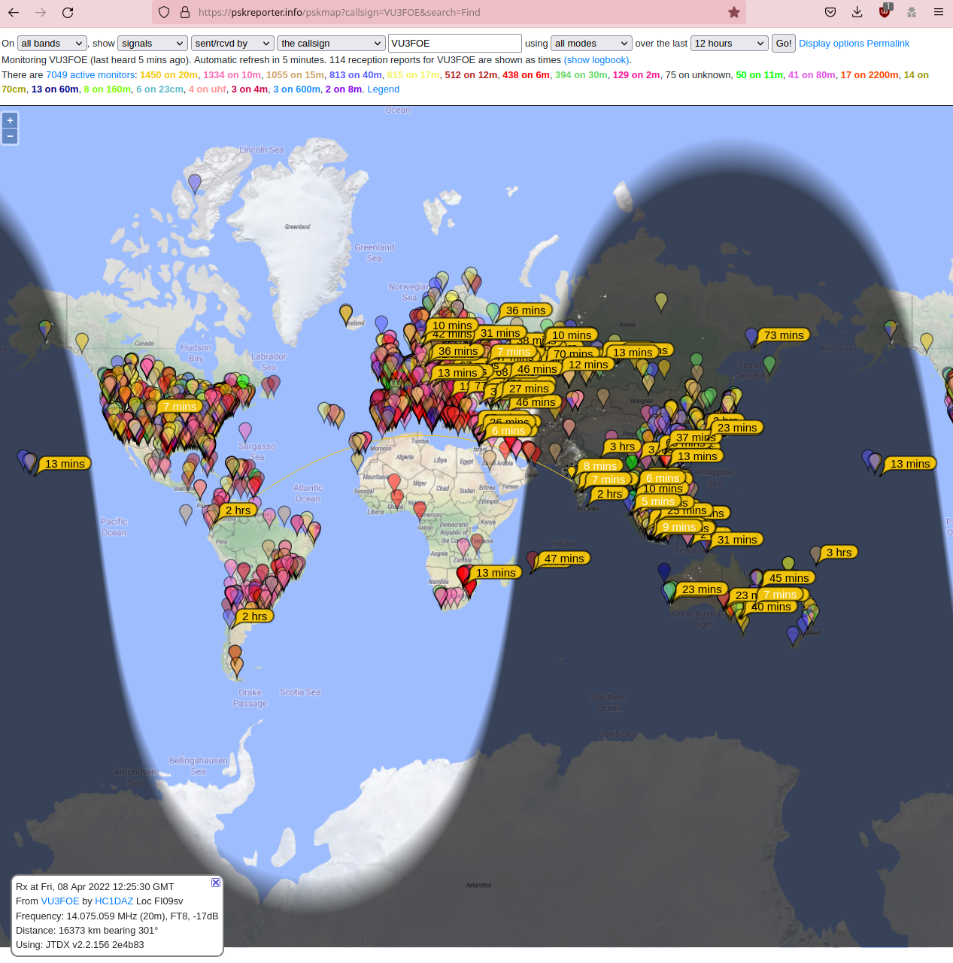
screenshots/6W-Screenshot_2022-04-08_20-03-49.png
