kholia/HF-PA-v6/screenshots/6W-Screenshot_2022-04-08_21-53-16.png

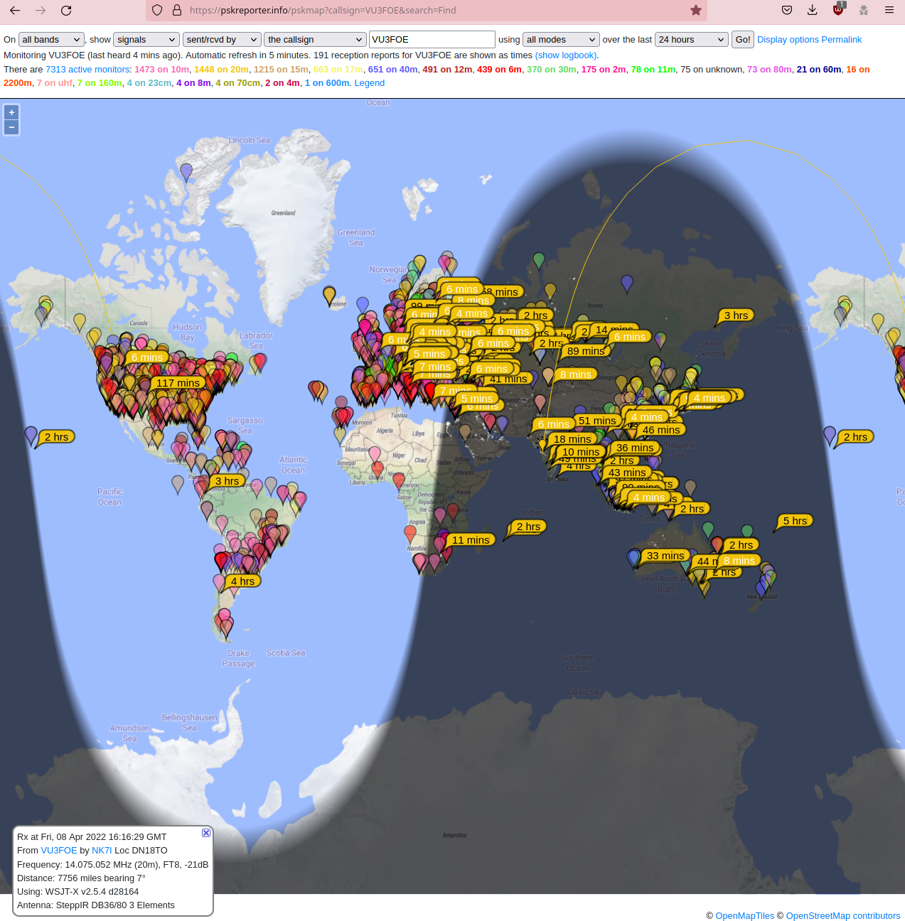
screenshots/6W-Screenshot_2022-04-08_21-53-16.png
