kholia/HF-PA-v6/screenshots/Screenshot_2022-04-08_21-43-46.png

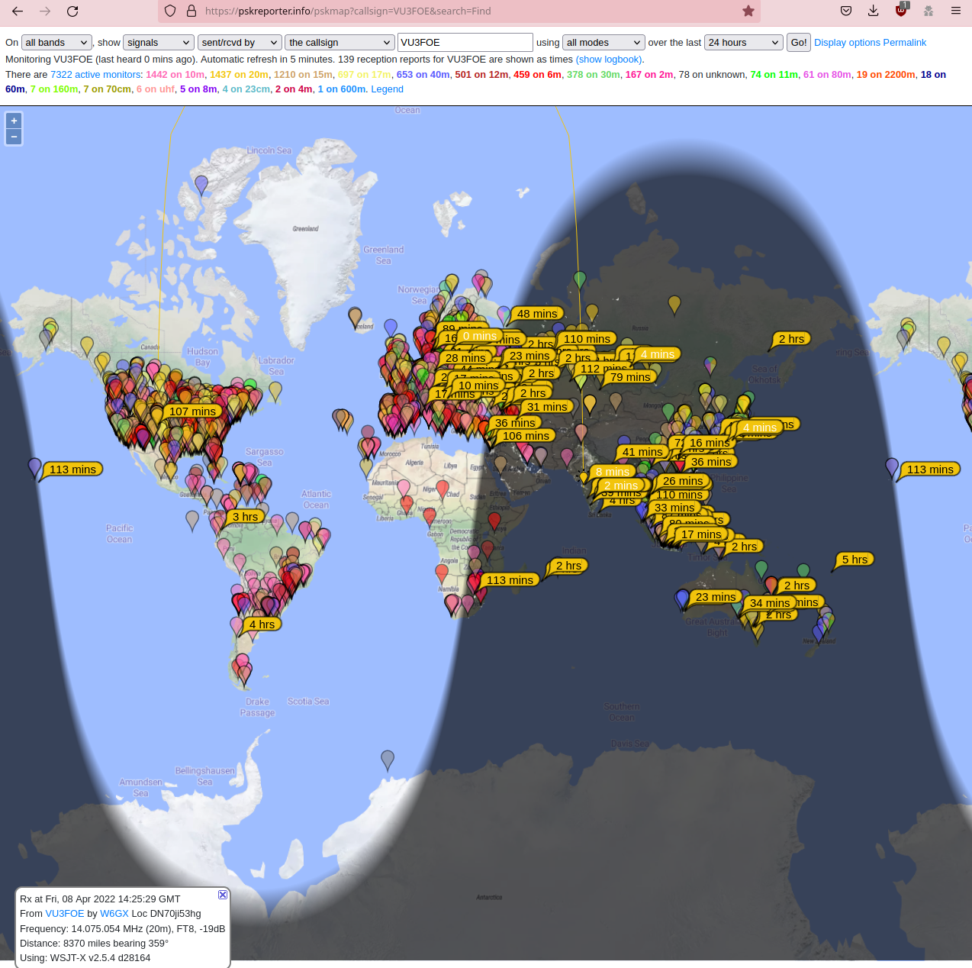
screenshots/Screenshot_2022-04-08_21-43-46.png
