kholia/HF-PA-v6/HF-PA-Combined/models/c-221789-1-e-3d.stp

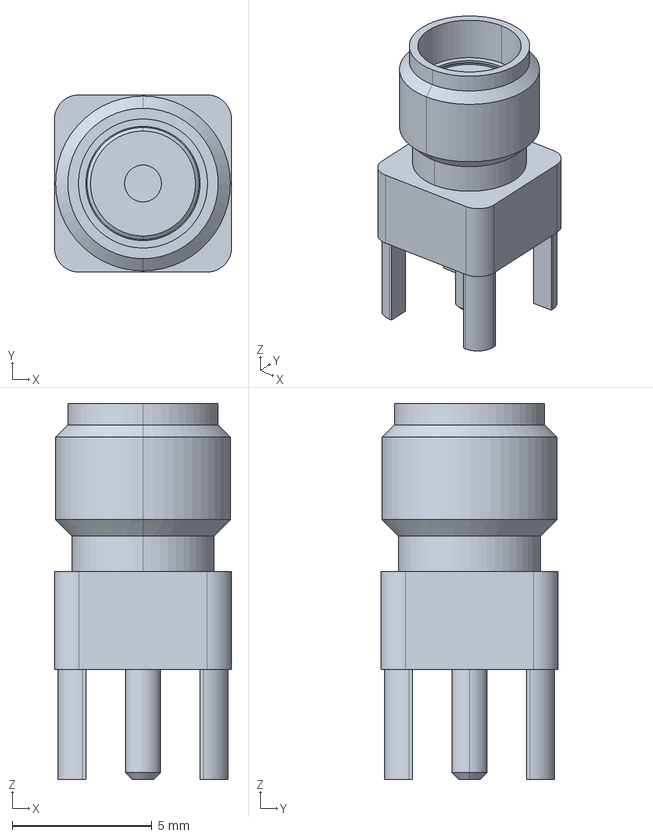
[picture p214: CAD file, 2022-05-05]
HF-PA-Combined/models/c-221789-1-e-3d.stp
6.35 x 6.35 x 13.5 mm
