kholia/HF-PA-v6/HF-PA-Combined/models/LM7805CT_NOPB.step

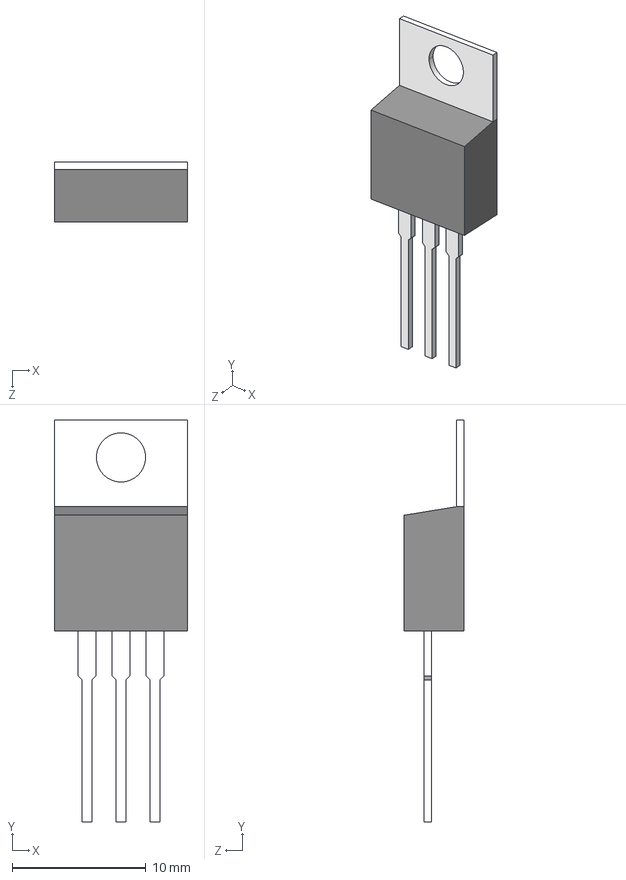
[picture p215: CAD file, 2022-05-05]
HF-PA-Combined/models/LM7805CT_NOPB.step
9.97 x 30.0 x 4.44 mm
