kholia/HF-PA-v6/HF-PA-Blocks/models/DC inductor.stl

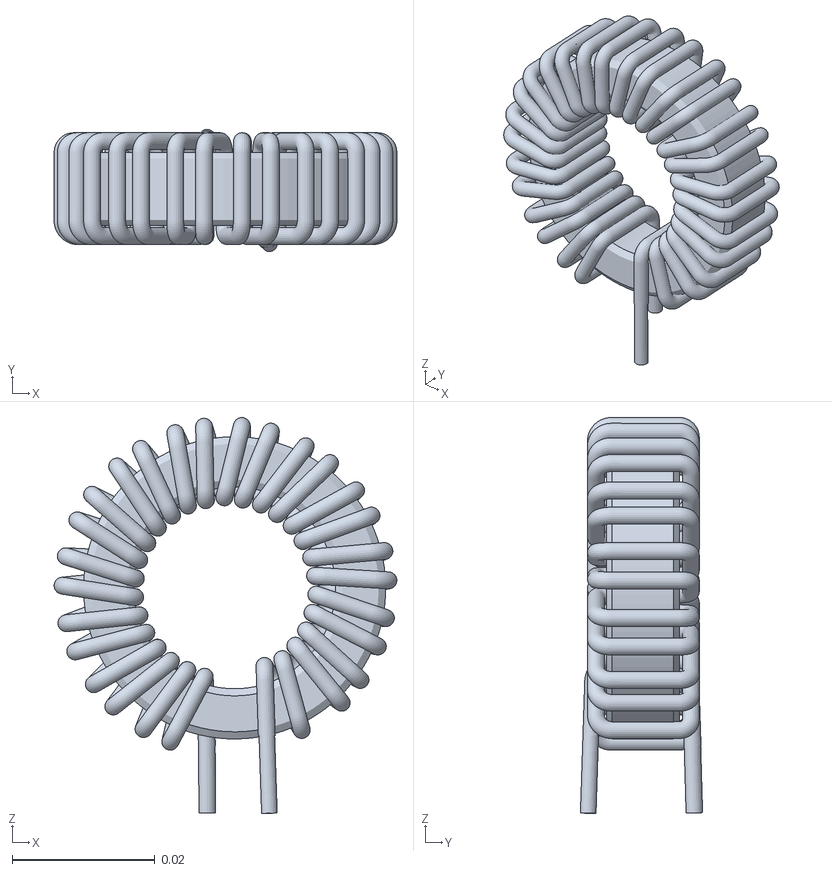
[picture p216: CAD file, 2022-05-05]
HF-PA-Blocks/models/DC inductor.stl
0.048 x 0.0171 x 0.0554
