kholia/HF-PA-v6/HF-PA-Blocks/models/R125.426.000 D.STEP

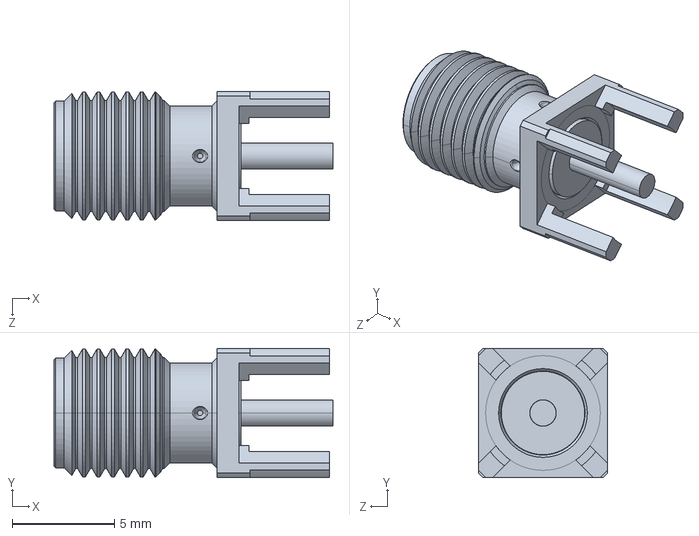
[picture p217: CAD file, 2022-05-05]
HF-PA-Blocks/models/R125.426.000 D.STEP
13.6 x 6.31 x 6.31 mm
