kholia/HF-PA-v6/Info/BS170-performance.png

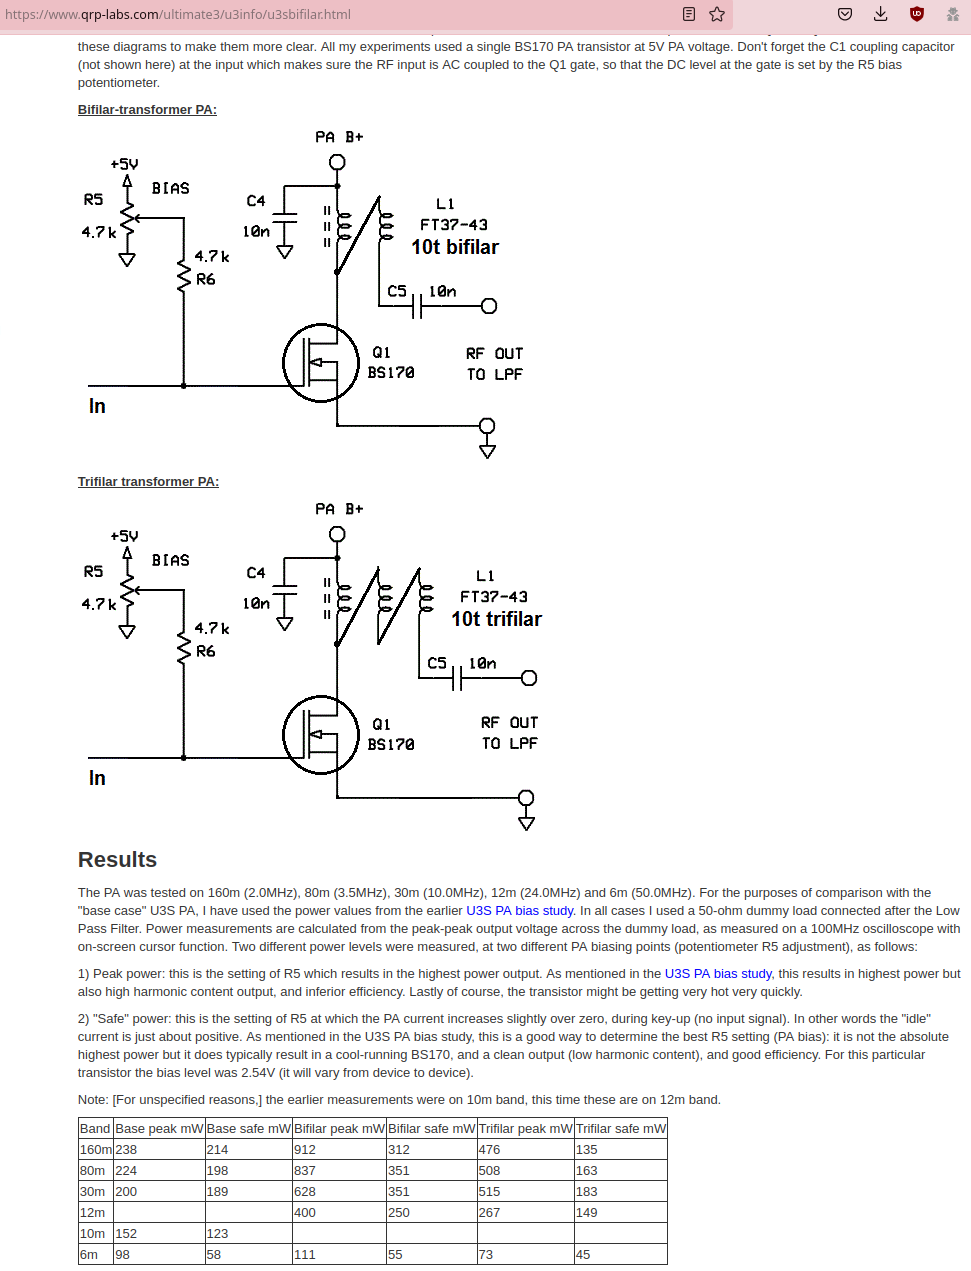
Info/BS170-performance.png
