kholia/HF-PA-v6/Finals.pdf

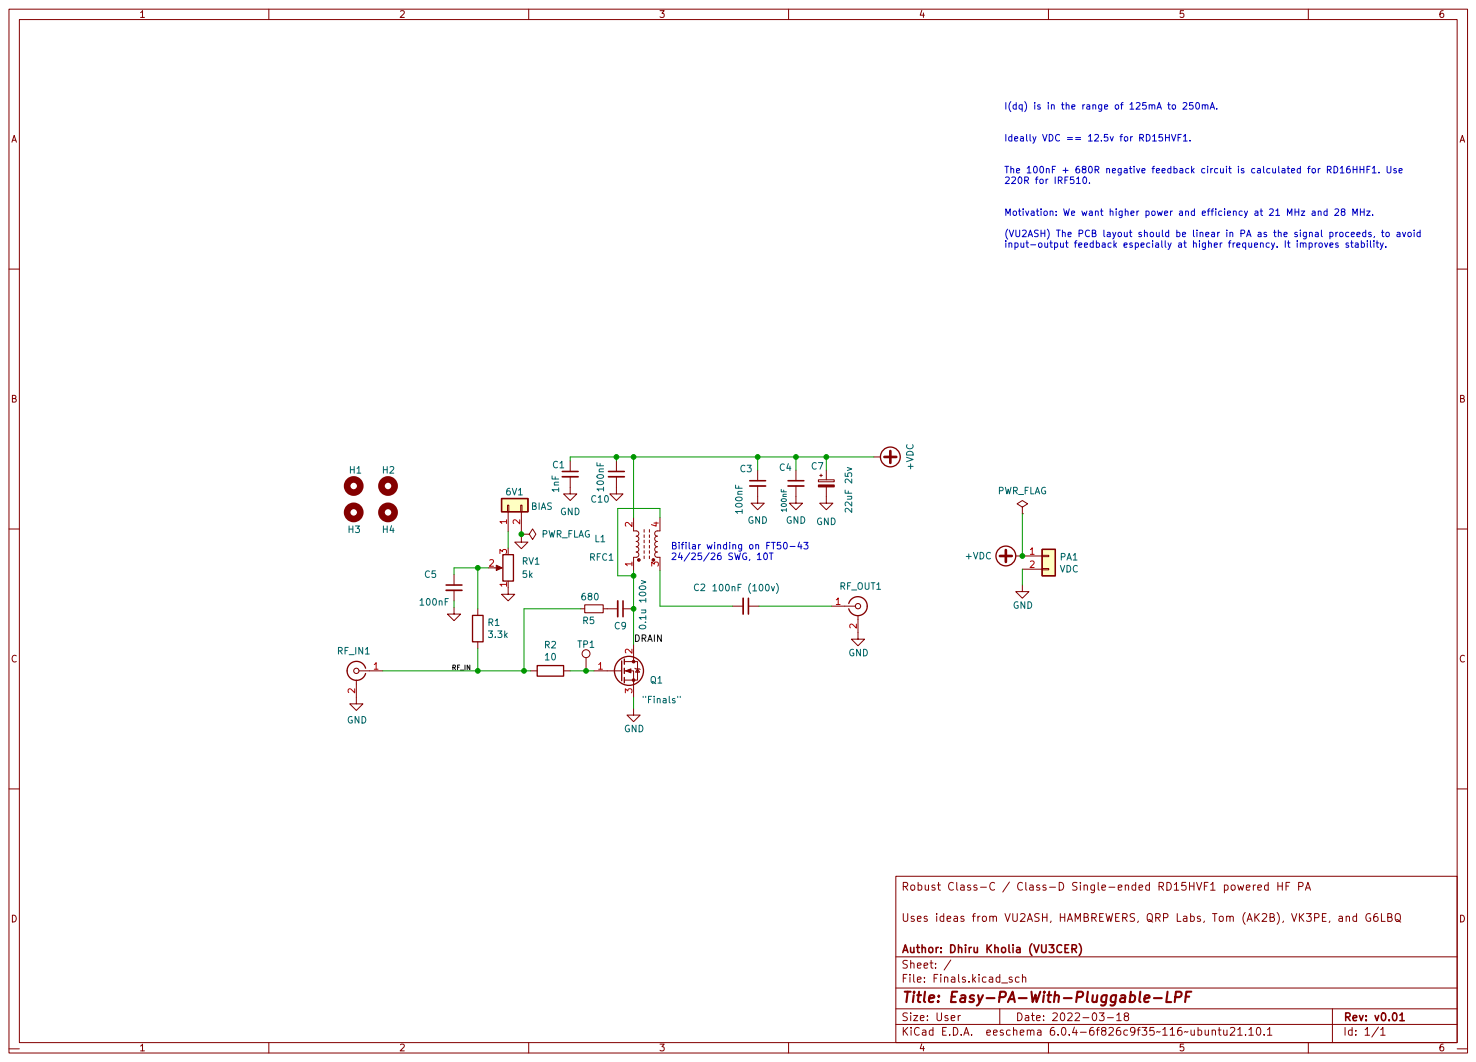
[picture p318: page 1]

I(dq) is in the range of 125mA to 250mA.

The 100nF + 680R negative feedback circuit is calculated for RD16HHF1. Use
220R for IRF510. Motivation: We want higher power and efficiency at 21 MHz and 28 MHz.

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

Robust Class-C / Class-D Single-ended RD15HVF1 powered HF PA

Uses ideas from VU2ASH, HAMBREWERS, QRP Labs, Tom (AK2B), VK3PE, and G6LBQ

File: Finals.kicad_sch Sheet: / Author: Dhiru Kholia (VU3CER)

Id: 1/1 Title: Easy-PA-With-Pluggable-LPF
