kholia/HF-PA-v6/HF-PA-Combined.pdf

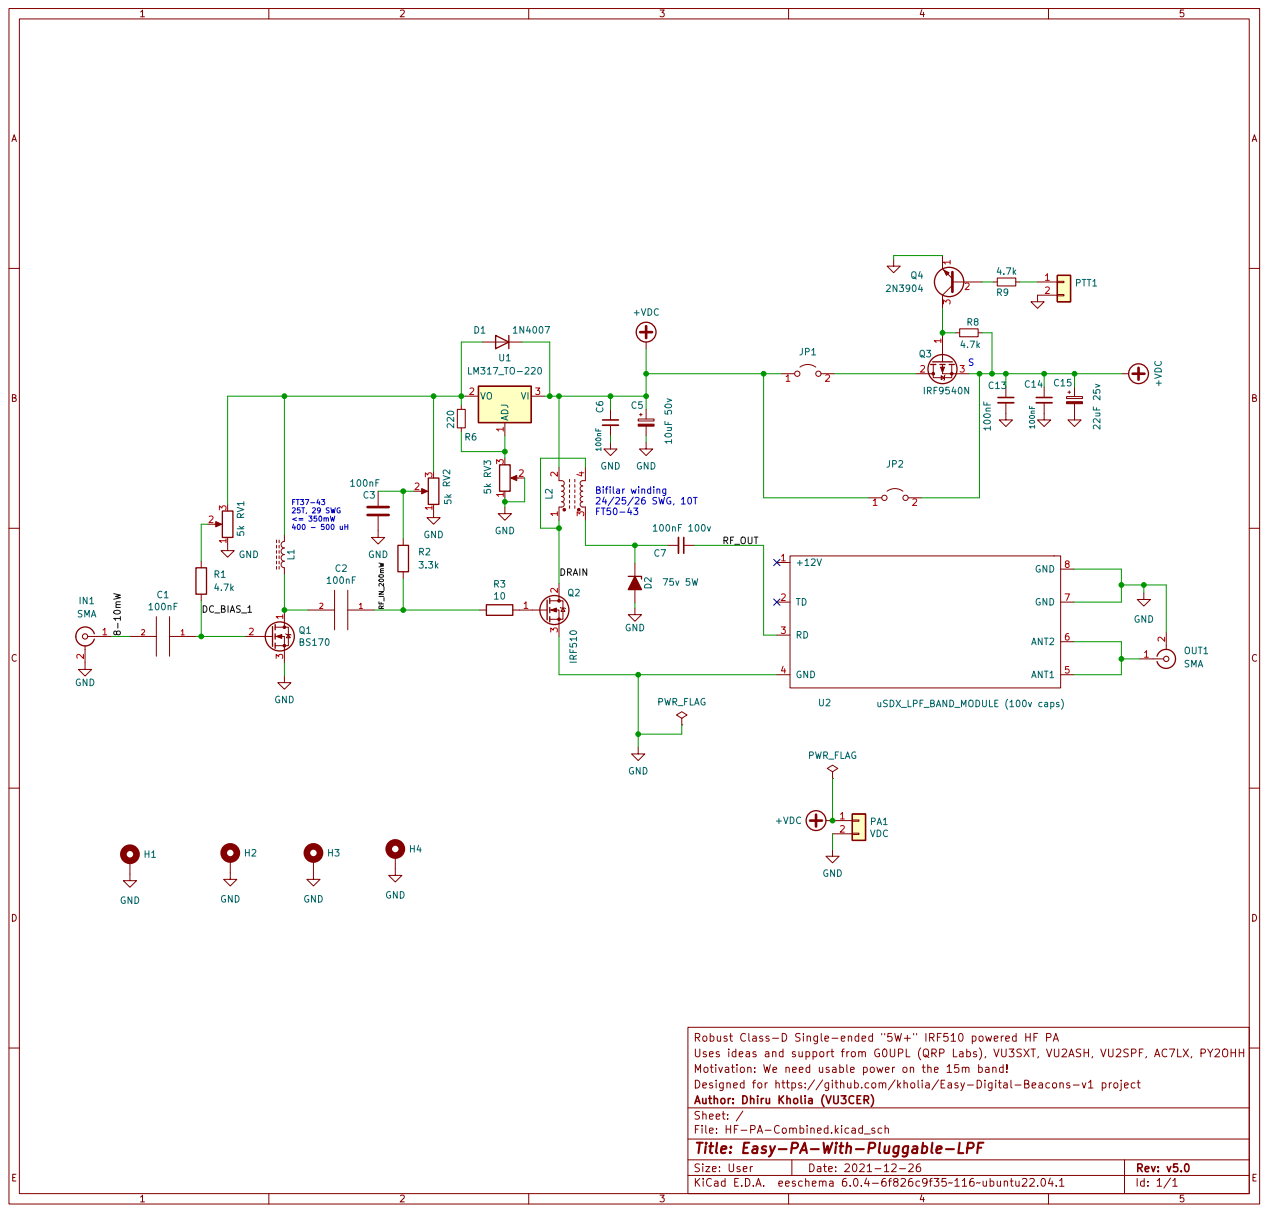
[picture p319: page 1]

2 3 Q2IRF510 +12V 1 TD 2 RD 3 GND 4 ANT1 5 ANT2 6 GND 7 GND 8 U2 uSDX_LPF_BAND_MODULE (100v caps) GND

Robust Class-D Single-ended "5W+" IRF510 powered HF PA
Uses ideas and support from G0UPL (QRP Labs), VU3SXT, VU2ASH, VU2SPF, AC7LX, PY2OHH
Motivation: We need usable power on the 15m band!
Designed for https://github.com/kholia/Easy-Digital-Beacons-v1 project
File: HF-PA-Combined.kicad_sch Sheet: / Author: Dhiru Kholia (VU3CER)

Id: 1/1 Title: Easy-PA-With-Pluggable-LPF
