kholia/HF-PA-v6/Power-v2.pdf

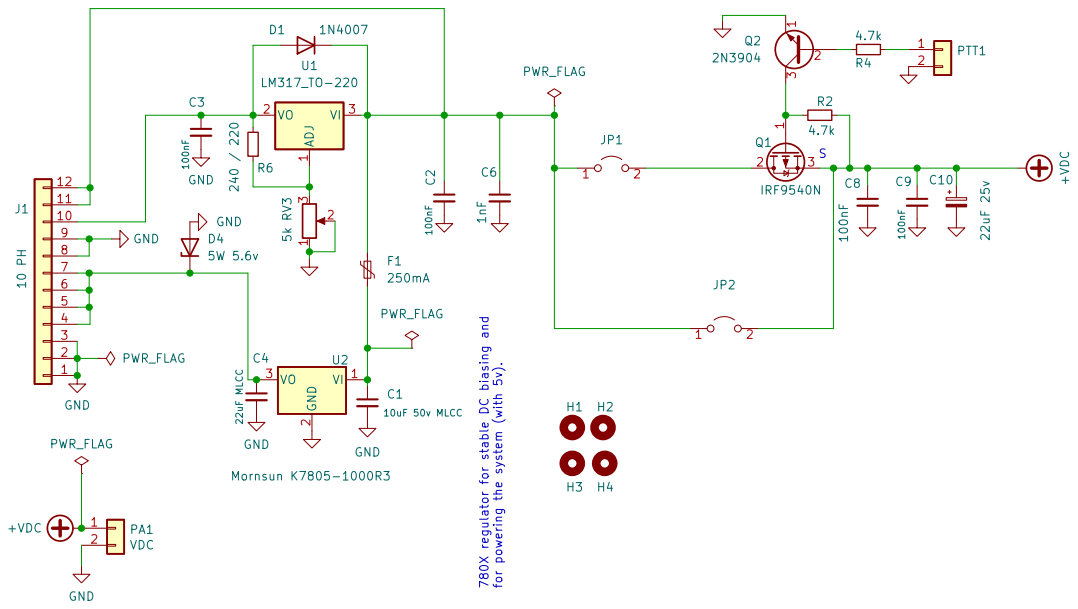
[picture p320: page 1]

File: Power-v2.kicad_sch Sheet: / Dhiru Kholia (VU3CER) H4

Id: 1/1 Title: Power Block
