kholia/HF-PA-v6/Power.pdf

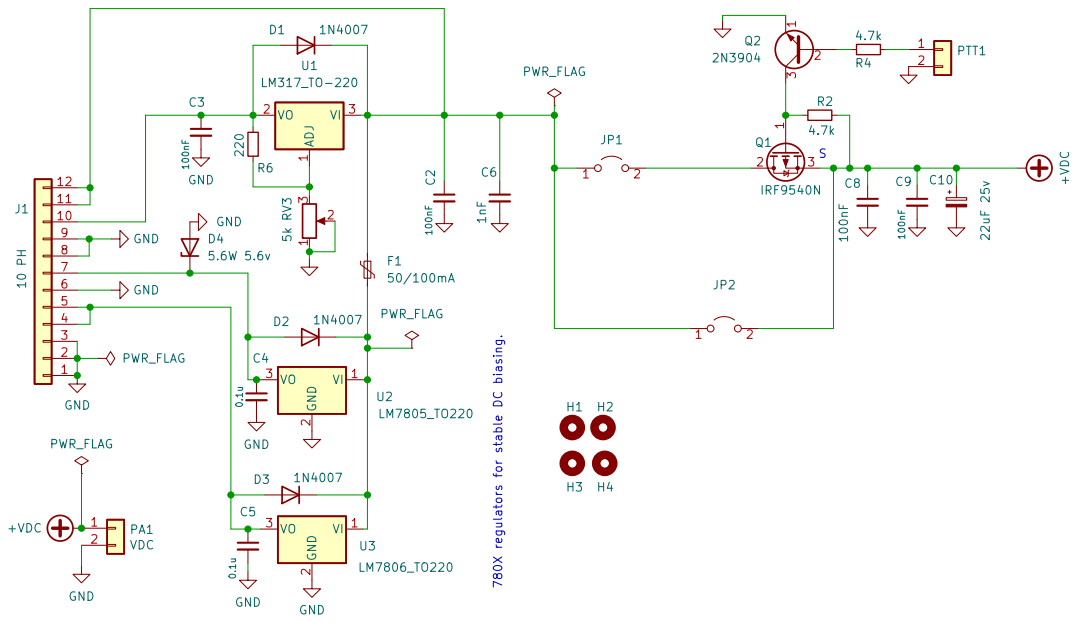
[picture p321: page 1]

3 RV3 5k S 780X regulators for stable DC biasing.

File: Power.kicad_sch Sheet: / Dhiru Kholia (VU3CER)

Id: 1/1 Title: Power Block
