kholia/HF-PA-v6/Info/qrp-power-amplifier.pdf

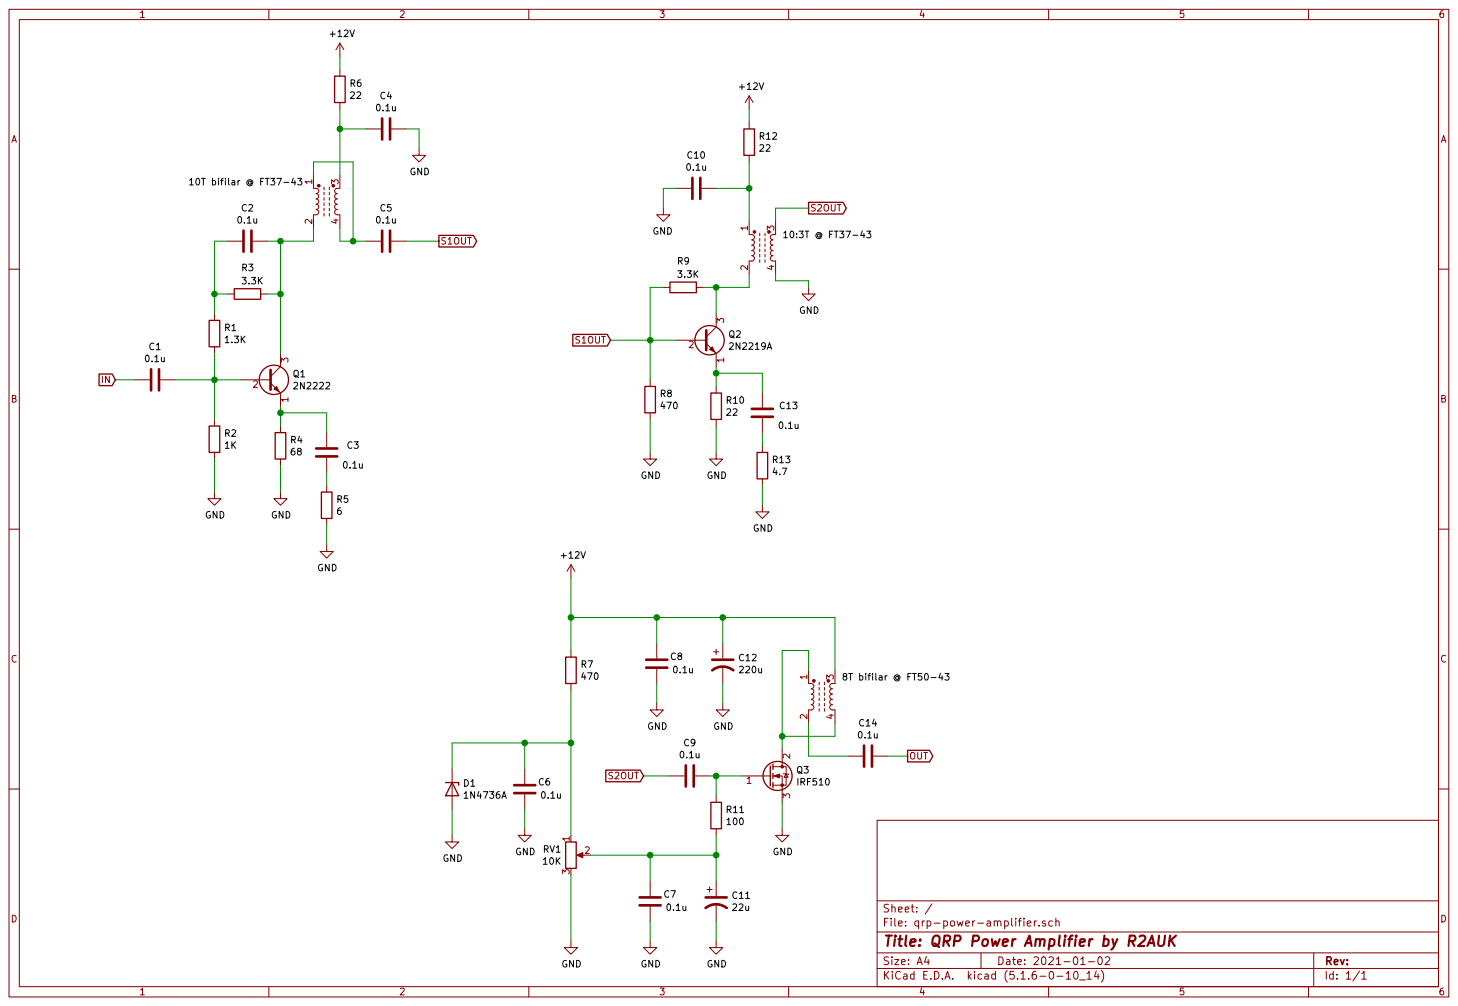
[picture p322: page 1]

File: qrp-power-amplifier.sch Sheet: /
Id: 1/1 Title: QRP Power Amplifier by R2AUK
