kholia/HF-PA-v6/Simulations/BS170-Driver.asc

C1: cap; 100nF
C4: cap; 100nF
L2: ind; 470µH
M2: nmos; BS170
R1: res; 50
R4: res; 4.7k
U2: potentiometer; Rt=5K set=.20
V1: voltage; PULSE(0 3.3 0 0.1p 0.1p 71ns 142ns)
V2: voltage; 29
V3: voltage; 12
Named nets: W1, 0, Vp, Vb
.lib bs170.lib
.tran 2500us
35ns 70ns  <-> 71ns 142ns
