kholia/HF-PA-v6/Simulations/New-PA-v1.asc

C1: cap; 100nF
C2: cap; 100nF
C3: cap; 1µF
C4: cap; 100nF
L1: ind; 400µH
L2: ind; 470µH
M1: nmos; IRF510
M2: nmos; BS170
R1: res; 3.3k
R2: res; 10
R3: res; 50
R4: res; 4.7k
U1: potentiometer; Rt=10K set=.65
U2: potentiometer
V1: voltage; PULSE(0 6 0 0.1p 0.1p 35ns 70ns)
V2: voltage; 29
V3: voltage; 12
Named nets: W1, Vp, 0, Vb
.lib bs170.lib
.tran 1000us
.inc RD16HHF1.txt
